whitfijs-jw/Volvo240-DigitalDash/QtDash/140 Ralleye Gauges/140-5ga-kmh-set.jpg

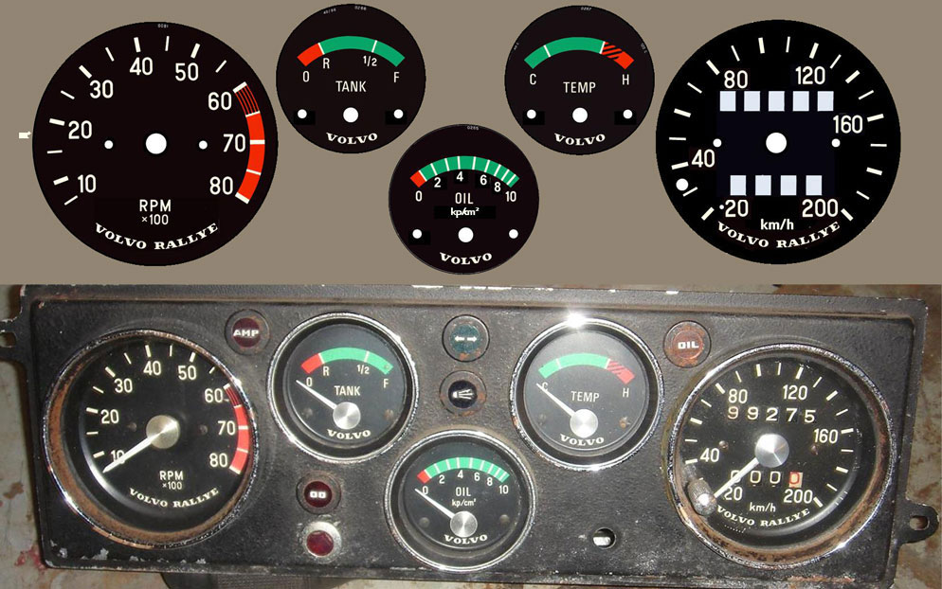
QtDash/140 Ralleye Gauges/140-5ga-kmh-set.jpg
