whitfijs-jw/Volvo240-DigitalDash/QtDash/140 Ralleye Gauges/140-5ga-mph-set.jpg

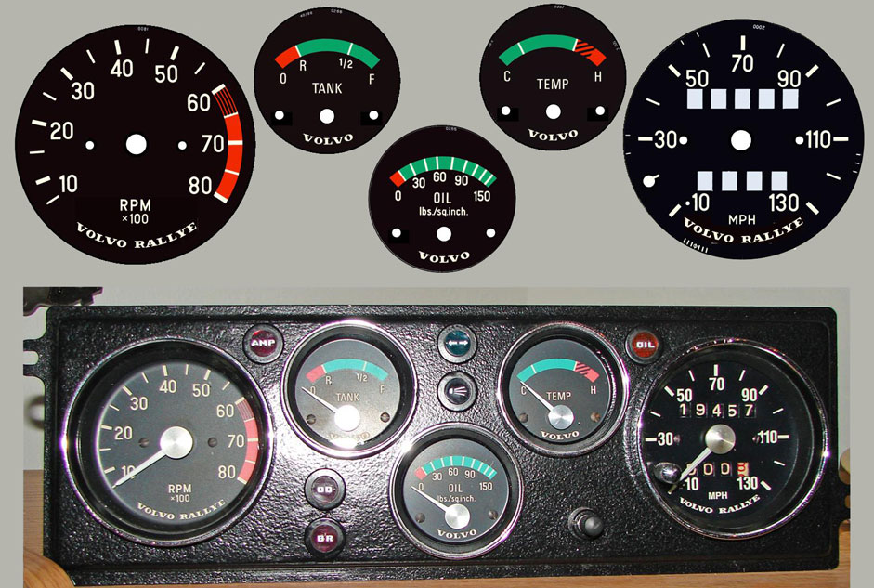
QtDash/140 Ralleye Gauges/140-5ga-mph-set.jpg
