whitfijs-jw/Volvo240-DigitalDash/QtDash/140 Ralleye Gauges/140-rallye-voltmeter.png

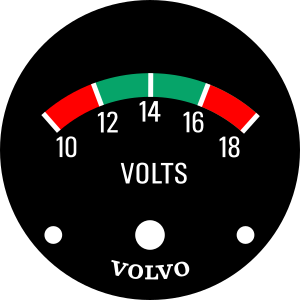
QtDash/140 Ralleye Gauges/140-rallye-voltmeter.png
