whitfijs-jw/Volvo240-DigitalDash/QtDash/240 gauges/81-85_240_220kmh04lo.png

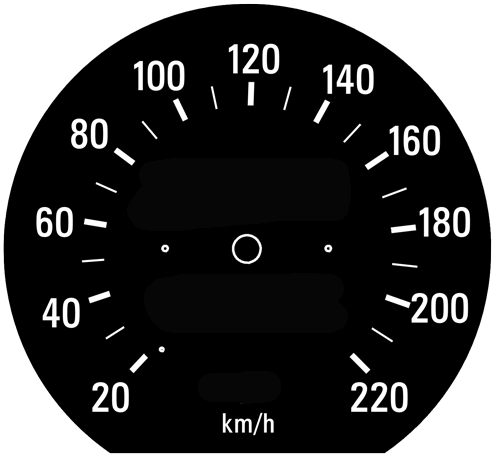
QtDash/240 gauges/81-85_240_220kmh04lo.png
