whitfijs-jw/Volvo240-DigitalDash/QtDash/240 gauges/early200kmhspeedolo.png

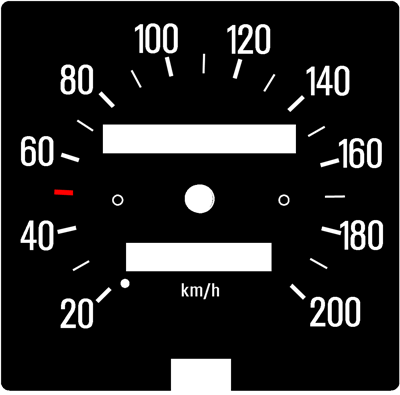
QtDash/240 gauges/early200kmhspeedolo.png
