whitfijs-jw/Volvo240-DigitalDash/QtDash/240 gauges/early-240-temp-fuel-overlay.png

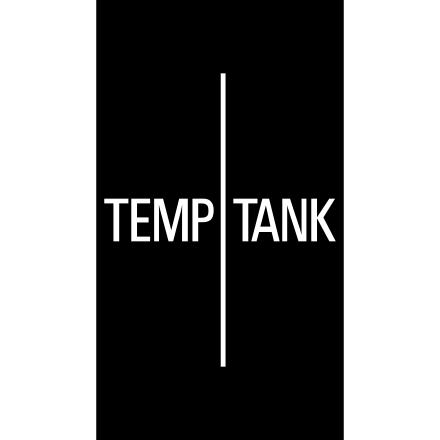
QtDash/240 gauges/early-240-temp-fuel-overlay.png
