whitfijs-jw/Volvo240-DigitalDash/QtDash/240 gauges/later-240-speedo-kph.png

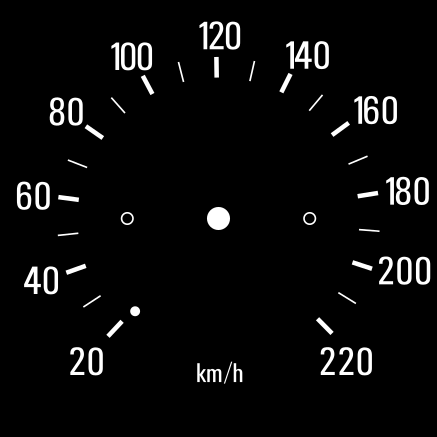
QtDash/240 gauges/later-240-speedo-kph.png
