whitfijs-jw/Volvo240-DigitalDash/QtDash/544 Gauges/oil-pressure-544-psi.png

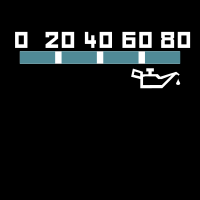
QtDash/544 Gauges/oil-pressure-544-psi.png
