whitfijs-jw/Volvo240-DigitalDash/QtDash/544 Gauges/PV-gaugecluster4-remote.jpg

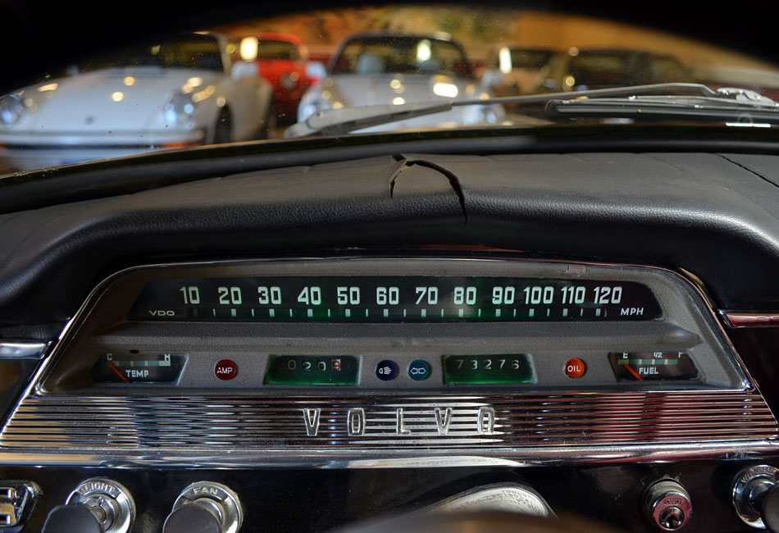
QtDash/544 Gauges/PV-gaugecluster4-remote.jpg
