whitfijs-jw/Volvo240-DigitalDash/QtDash/544 Gauges/s-l1600.jpg

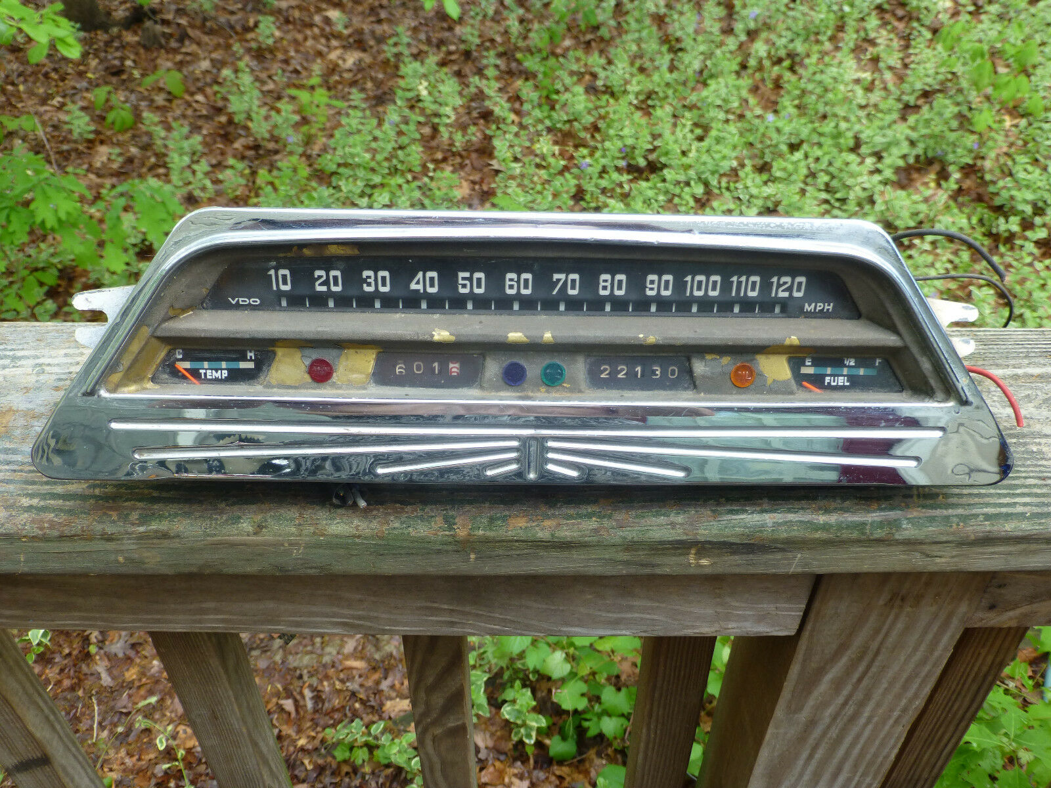
QtDash/544 Gauges/s-l1600.jpg
