whitfijs-jw/Volvo240-DigitalDash/QtDash/850R gauges/white_faces.jpg

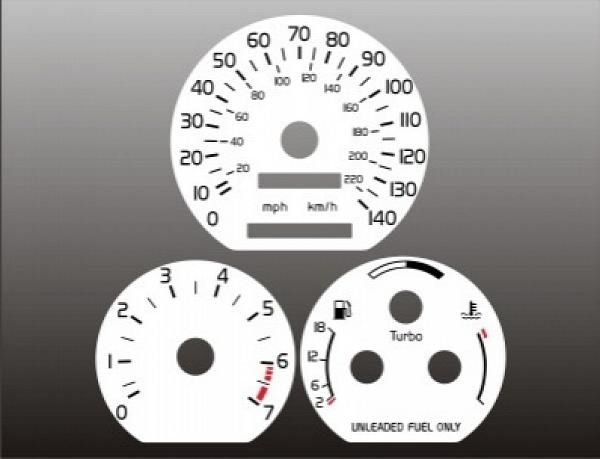
QtDash/850R gauges/white_faces.jpg
