whitfijs-jw/Volvo240-DigitalDash/QtDash/850R gauges/whole-dash.jpeg

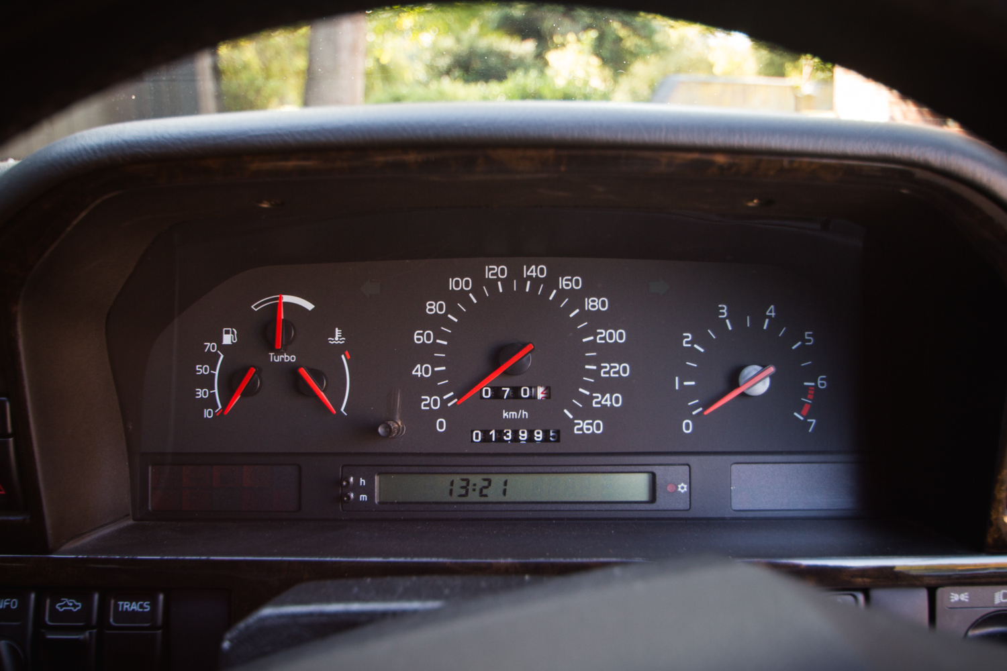
QtDash/850R gauges/whole-dash.jpeg
