whitfijs-jw/Volvo240-DigitalDash/QtDash/940 Gauges/740_boost.png

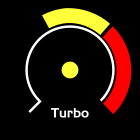
QtDash/940 Gauges/740_boost.png
