whitfijs-jw/Volvo240-DigitalDash/QtDash/940 Gauges/740_coolant_temp.png

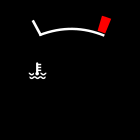
QtDash/940 Gauges/740_coolant_temp.png
