whitfijs-jw/Volvo240-DigitalDash/QtDash/940 Gauges/740_speedo_recreation.png

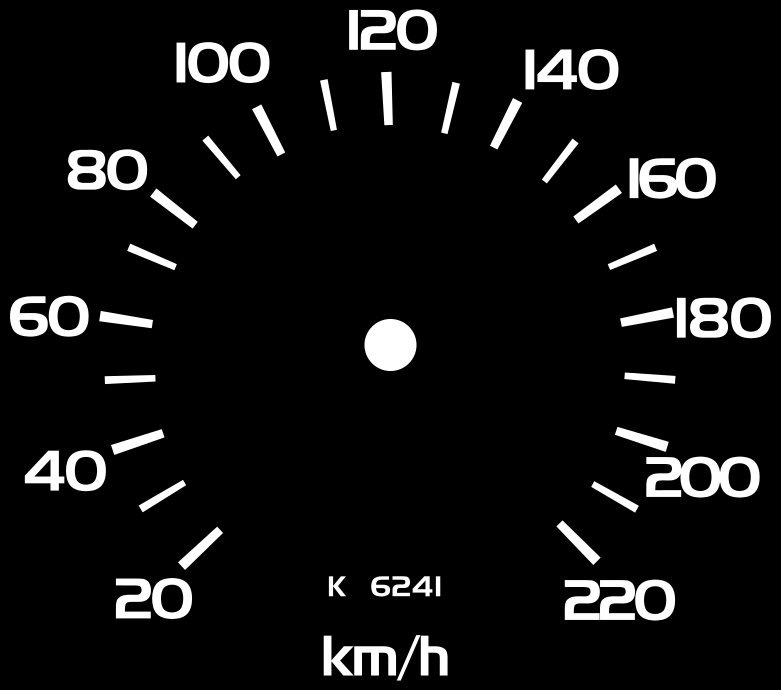
QtDash/940 Gauges/740_speedo_recreation.png
