whitfijs-jw/Volvo240-DigitalDash/QtDash/940 Gauges/740_tach.png

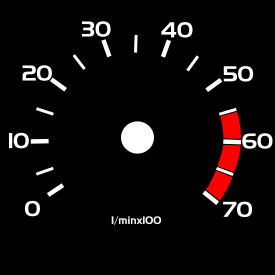
QtDash/940 Gauges/740_tach.png
