whitfijs-jw/Volvo240-DigitalDash/QtDash/940 Gauges/740_whole_dash.jpg

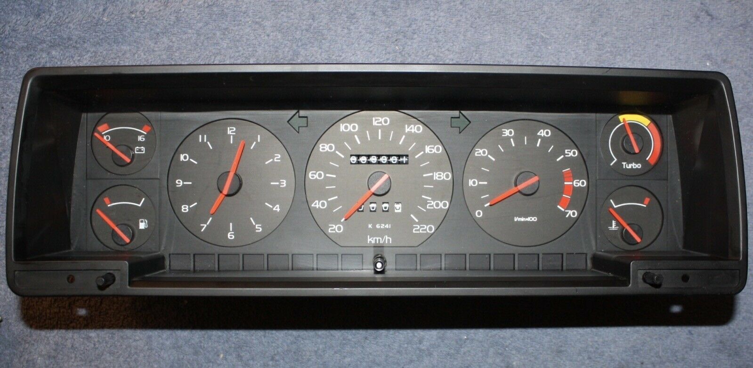
QtDash/940 Gauges/740_whole_dash.jpg
