whitfijs-jw/Volvo240-DigitalDash/QtDash/940 Gauges/940_turbo_cluster.png

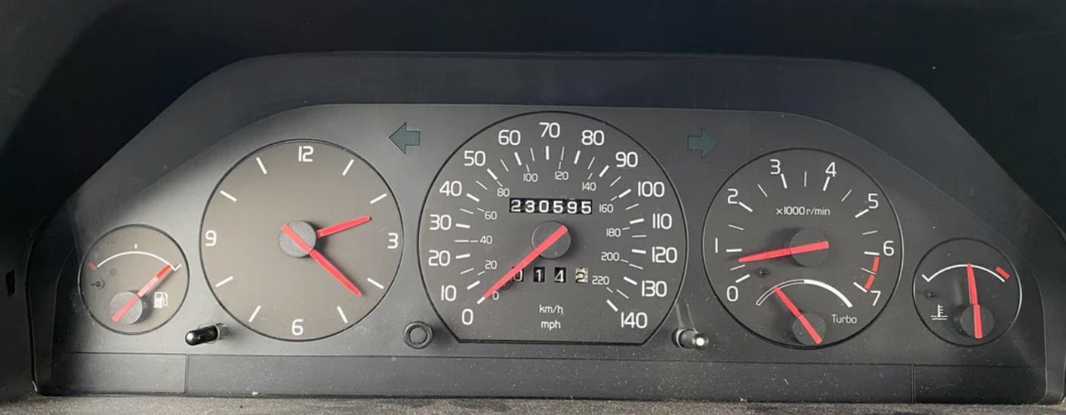
QtDash/940 Gauges/940_turbo_cluster.png
