whitfijs-jw/Volvo240-DigitalDash/QtDash/940 Gauges/clock_940.jpg

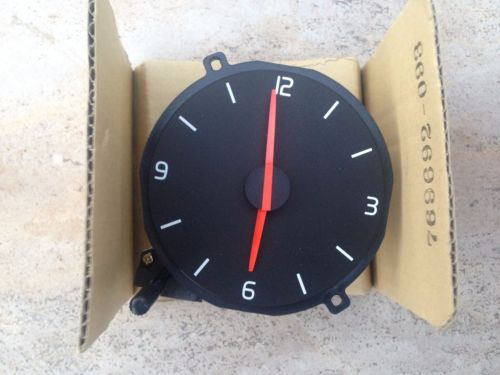
QtDash/940 Gauges/clock_940.jpg
