whitfijs-jw/Volvo240-DigitalDash/QtDash/940 Gauges/speedo4.JPG

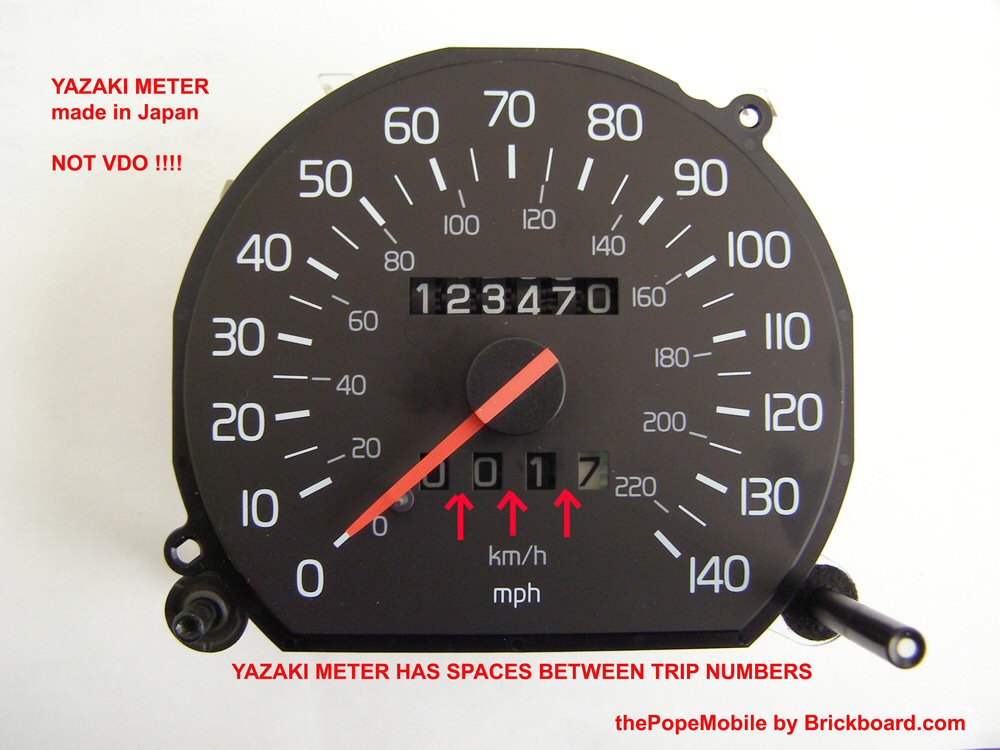
QtDash/940 Gauges/speedo4.JPG
