whitfijs-jw/Volvo240-DigitalDash/QtDash/940 Gauges/speedo_940.jpg

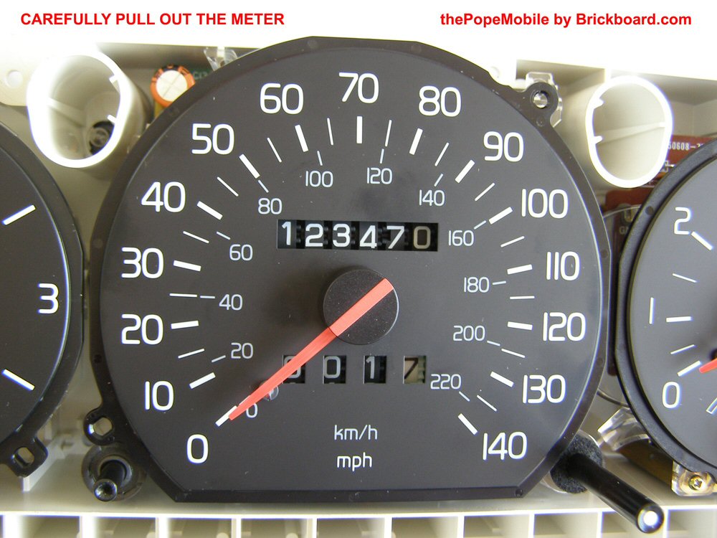
QtDash/940 Gauges/speedo_940.jpg
