whitfijs-jw/Volvo240-DigitalDash/QtDash/940 Gauges/whole_dash.jpeg

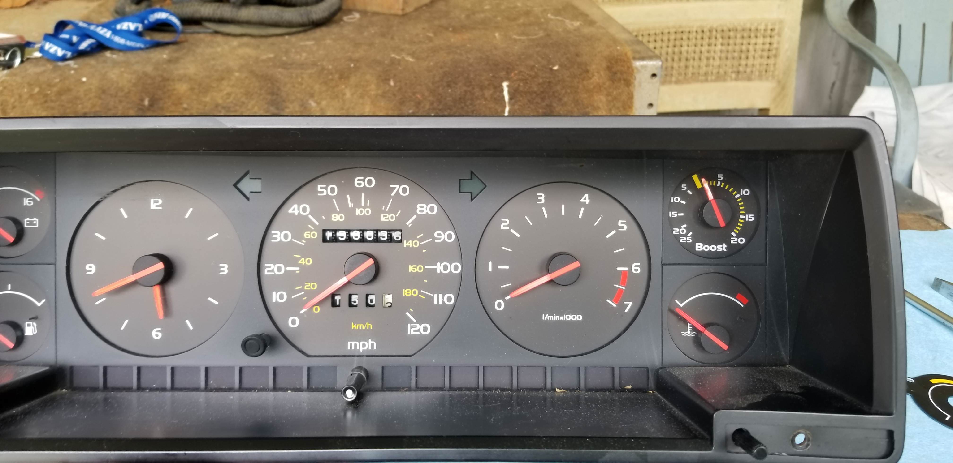
QtDash/940 Gauges/whole_dash.jpeg
