whitfijs-jw/Volvo240-DigitalDash/QtDash/Hardware/Dash Pinouts/240instruments1980med.jpg

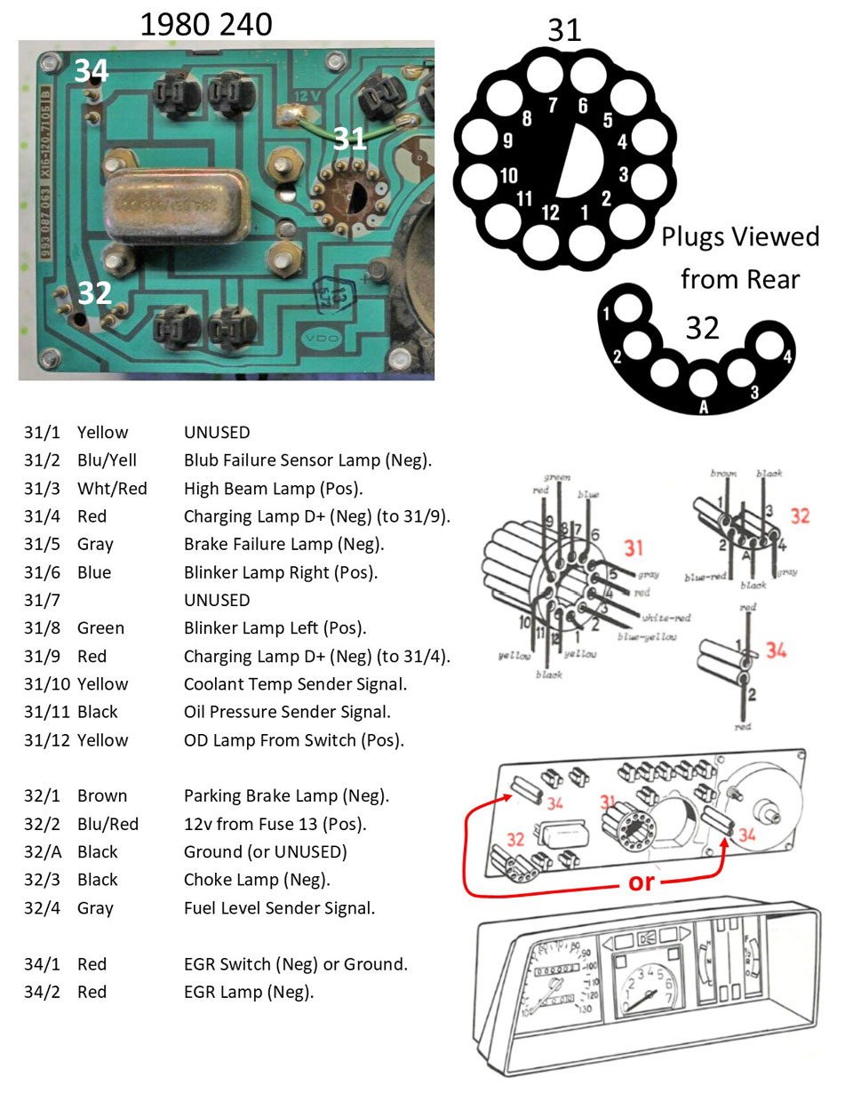
QtDash/Hardware/Dash Pinouts/240instruments1980med.jpg
