whitfijs-jw/Volvo240-DigitalDash/QtDash/Hardware/Dash Pinouts/240instruments1984-01med.jpg

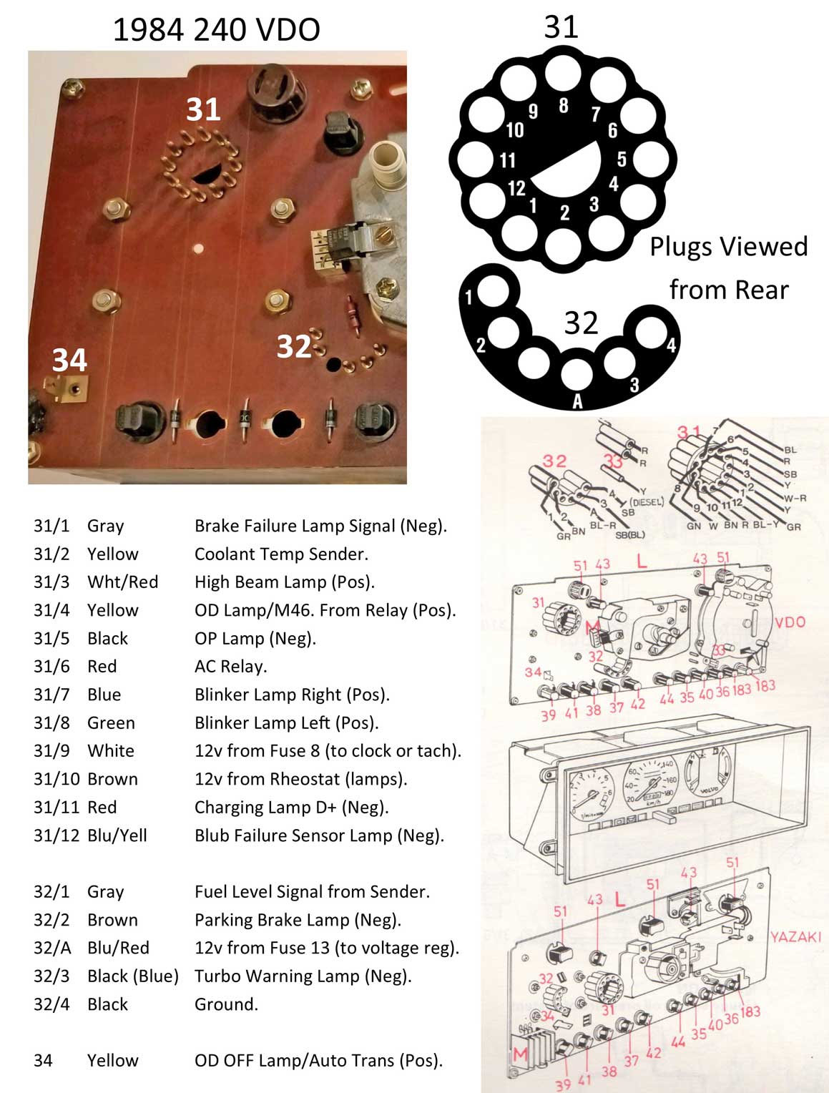
QtDash/Hardware/Dash Pinouts/240instruments1984-01med.jpg
