whitfijs-jw/Volvo240-DigitalDash/QtDash/Hardware/Dash Pinouts/240instruments1987-01med.jpg

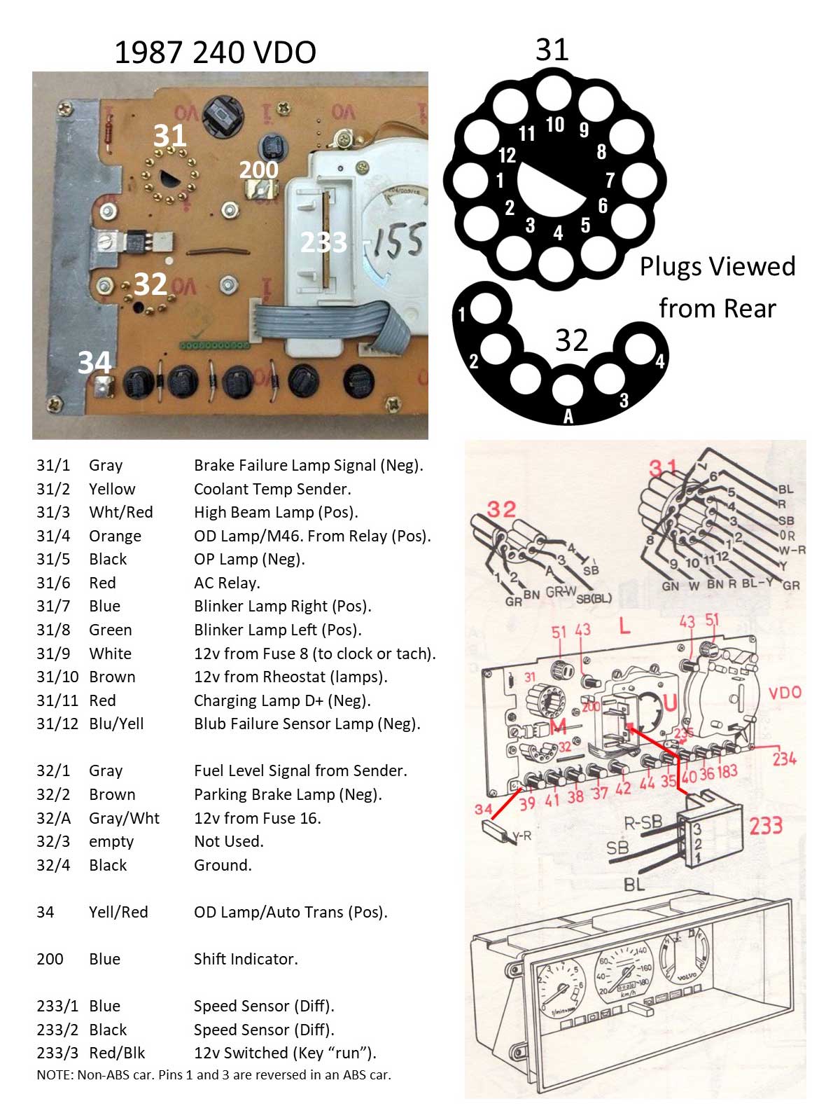
QtDash/Hardware/Dash Pinouts/240instruments1987-01med.jpg
