whitfijs-jw/Volvo240-DigitalDash/QtDash/Hardware/Dash Pinouts/240instruments1993-002med.jpg

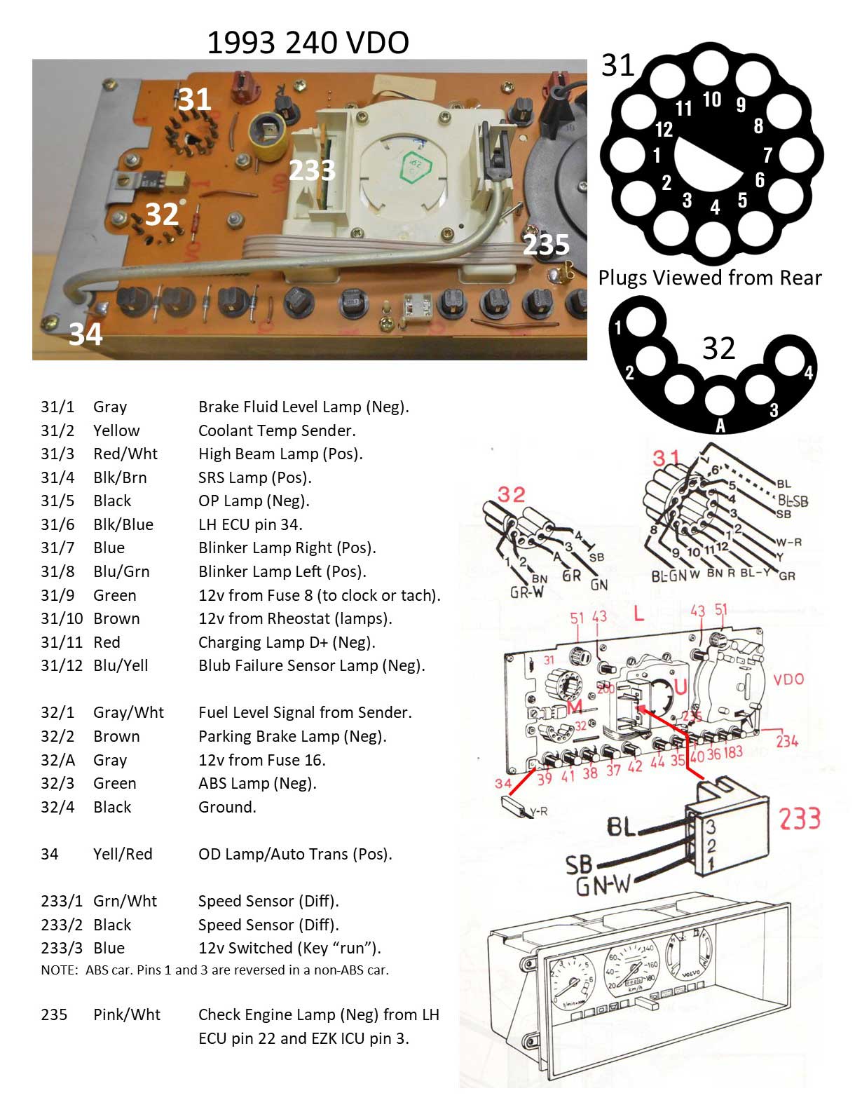
QtDash/Hardware/Dash Pinouts/240instruments1993-002med.jpg
