whitfijs-jw/Volvo240-DigitalDash/QtDash/Hardware/Dash Pinouts/240instruments-rsport-2med.jpg

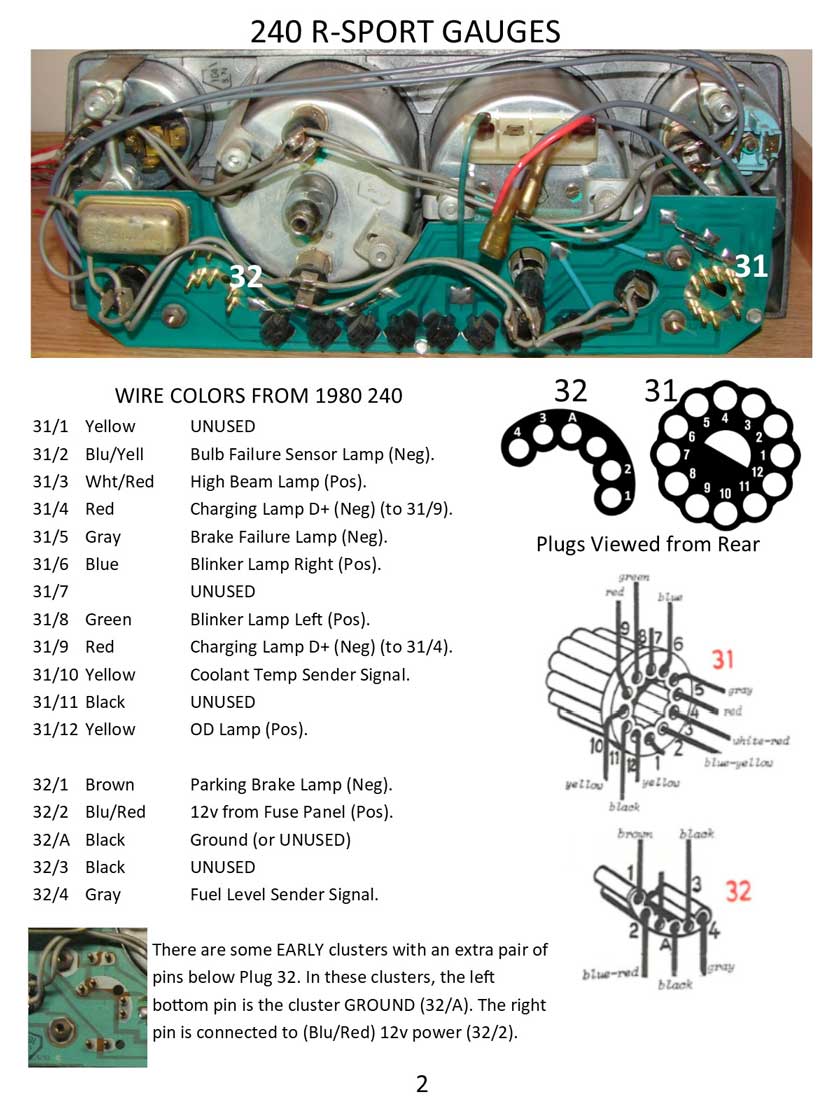
QtDash/Hardware/Dash Pinouts/240instruments-rsport-2med.jpg
