whitfijs-jw/Volvo240-DigitalDash/QtDash/Hardware/DashHat/Board Previews/Rev C/bottom.png

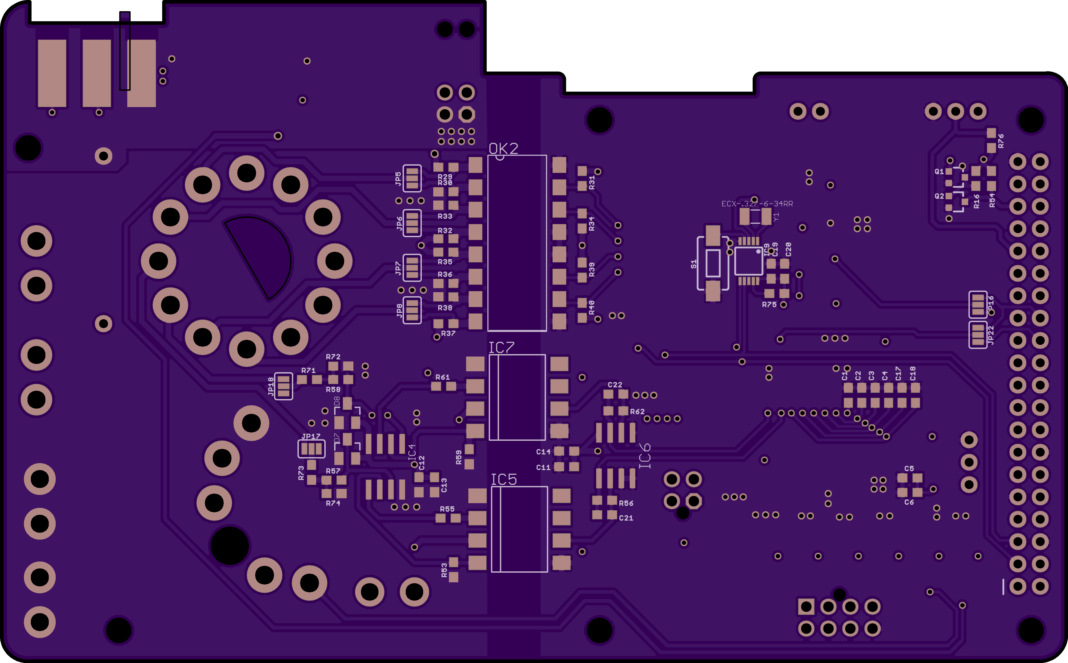
QtDash/Hardware/DashHat/Board Previews/Rev C/bottom.png
