whitfijs-jw/Volvo240-DigitalDash/QtDash/Hardware/DashHat/Board Previews/Rev C/top.png

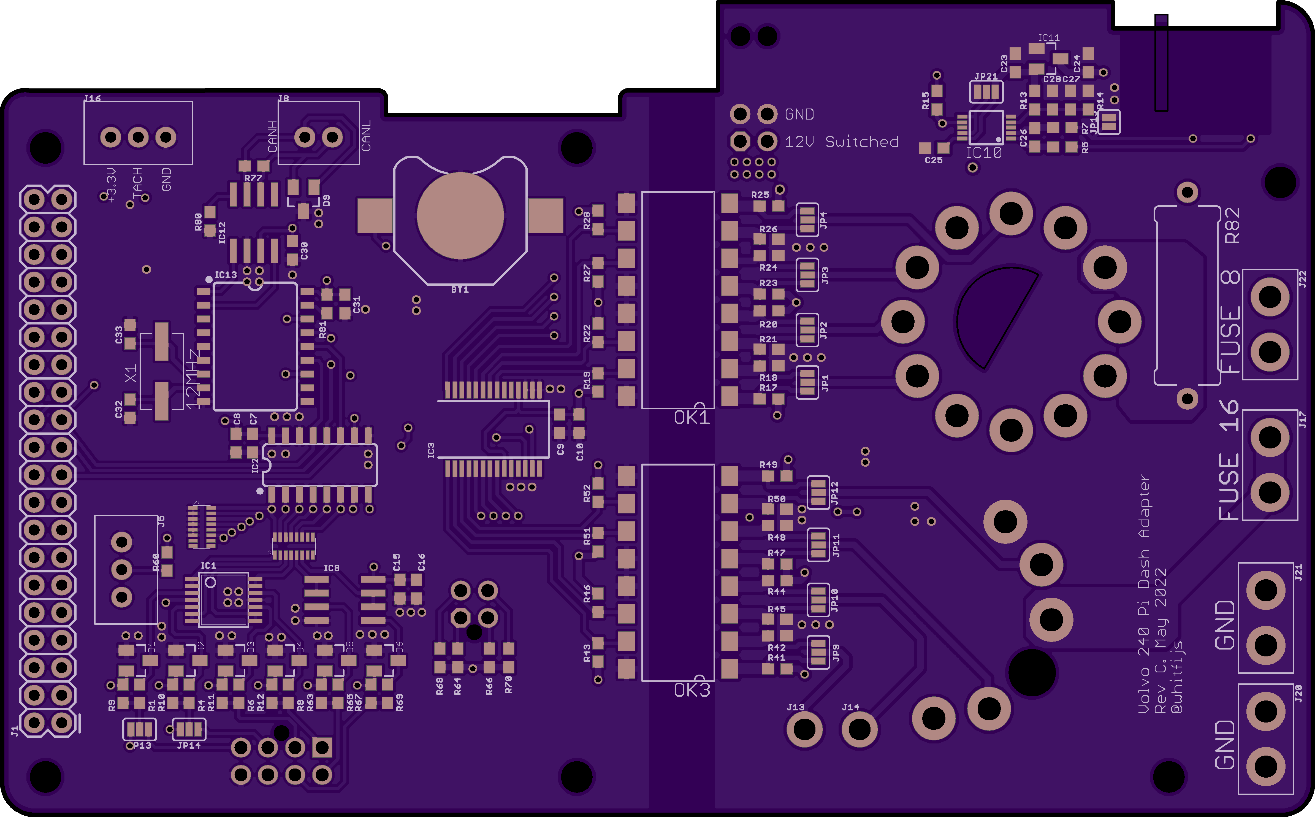
QtDash/Hardware/DashHat/Board Previews/Rev C/top.png
