whitfijs-jw/Volvo240-DigitalDash/QtDash/Hardware/Datasheets/Sensor Info/gm_MAP_sensors.gif

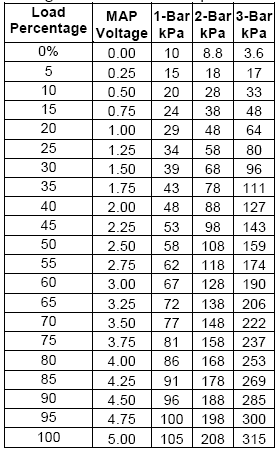
QtDash/Hardware/Datasheets/Sensor Info/gm_MAP_sensors.gif
