whitfijs-jw/Volvo240-DigitalDash/QtDash/Hardware/TouchPanel/3D Models/back_both_covers.png

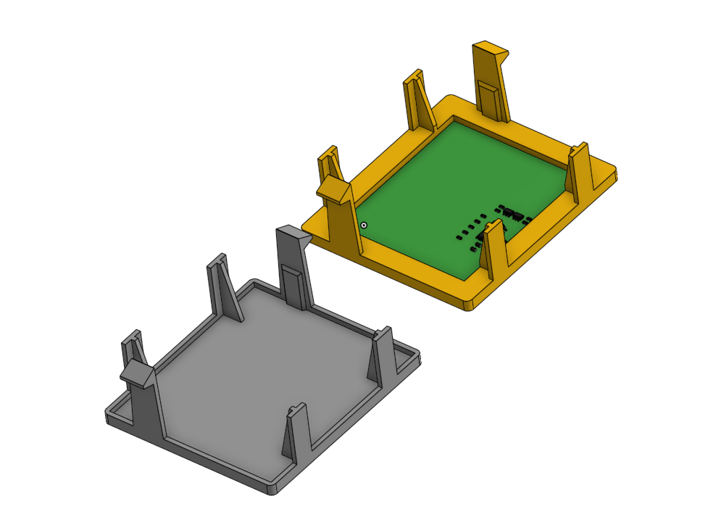
QtDash/Hardware/TouchPanel/3D Models/back_both_covers.png
