whitfijs-jw/Volvo240-DigitalDash/QtDash/Hardware/TouchPanel/touch_panel/bottom_layer.svg/g48.png

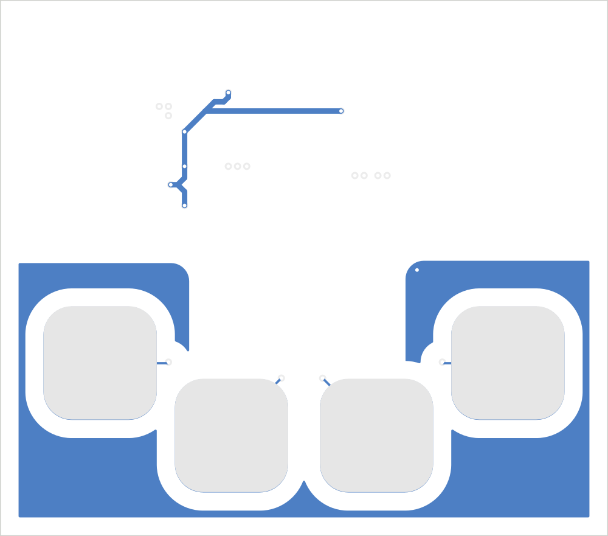
QtDash/Hardware/TouchPanel/touch_panel/bottom_layer.svg/g48.png
