whitfijs-jw/Volvo240-DigitalDash/QtDash/p1800 Gauges/2v2ucAjL2x37gRP.jpg

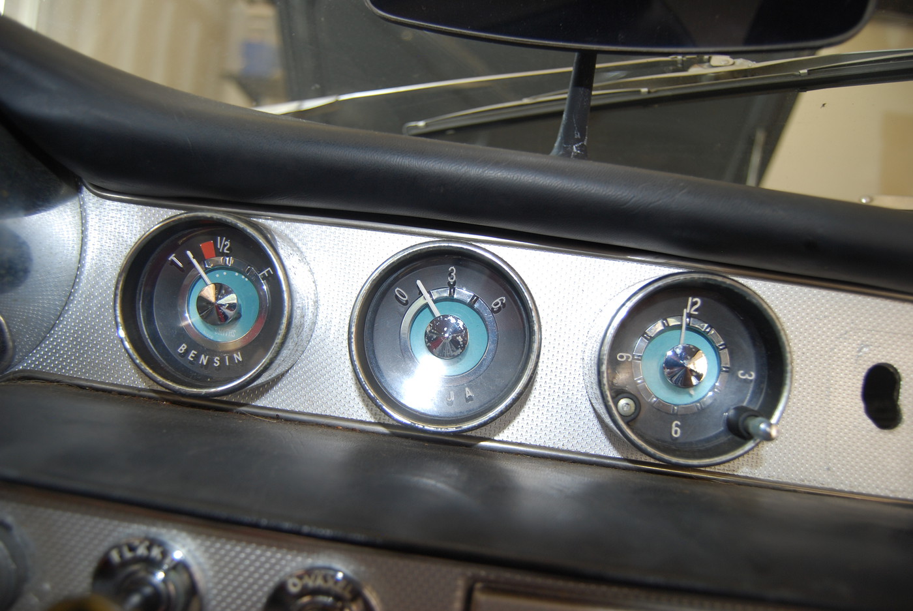
QtDash/p1800 Gauges/2v2ucAjL2x37gRP.jpg
