whitfijs-jw/Volvo240-DigitalDash/QtDash/p1800 Gauges/2v2ucBK9Ux37gRP.jpg

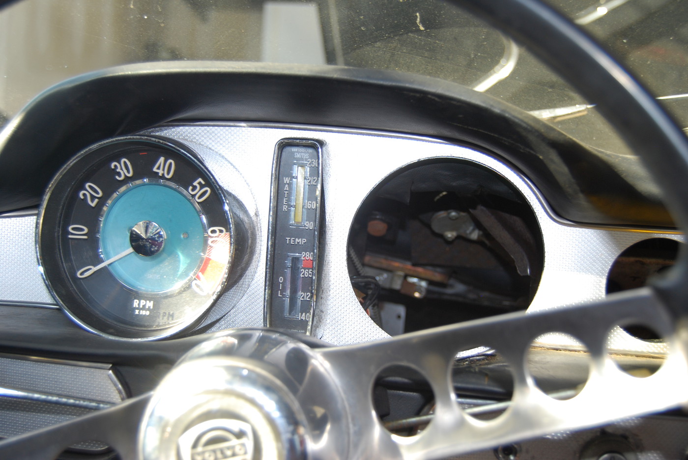
QtDash/p1800 Gauges/2v2ucBK9Ux37gRP.jpg
