whitfijs-jw/Volvo240-DigitalDash/QtDash/p1800 Gauges/1964-volvo-p1800-s-coupe-photo-board.jpg

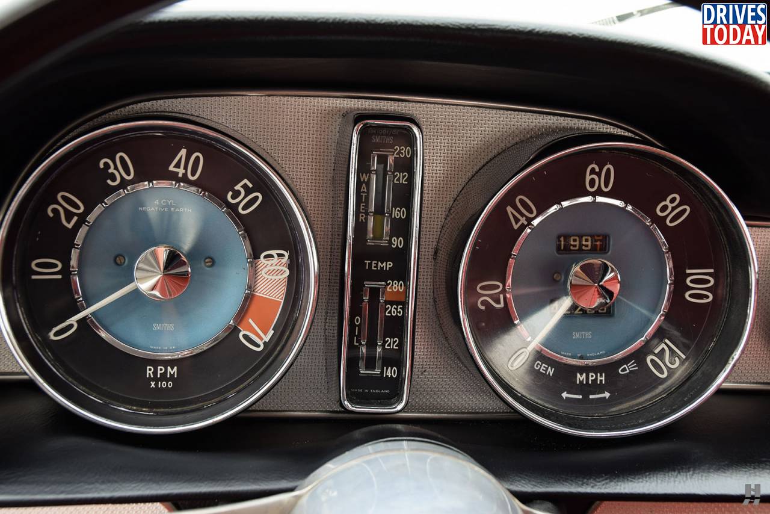
QtDash/p1800 Gauges/1964-volvo-p1800-s-coupe-photo-board.jpg
