whitfijs-jw/Volvo240-DigitalDash/QtDash/p1800 Gauges/1973-volvo-1800-es.jpeg

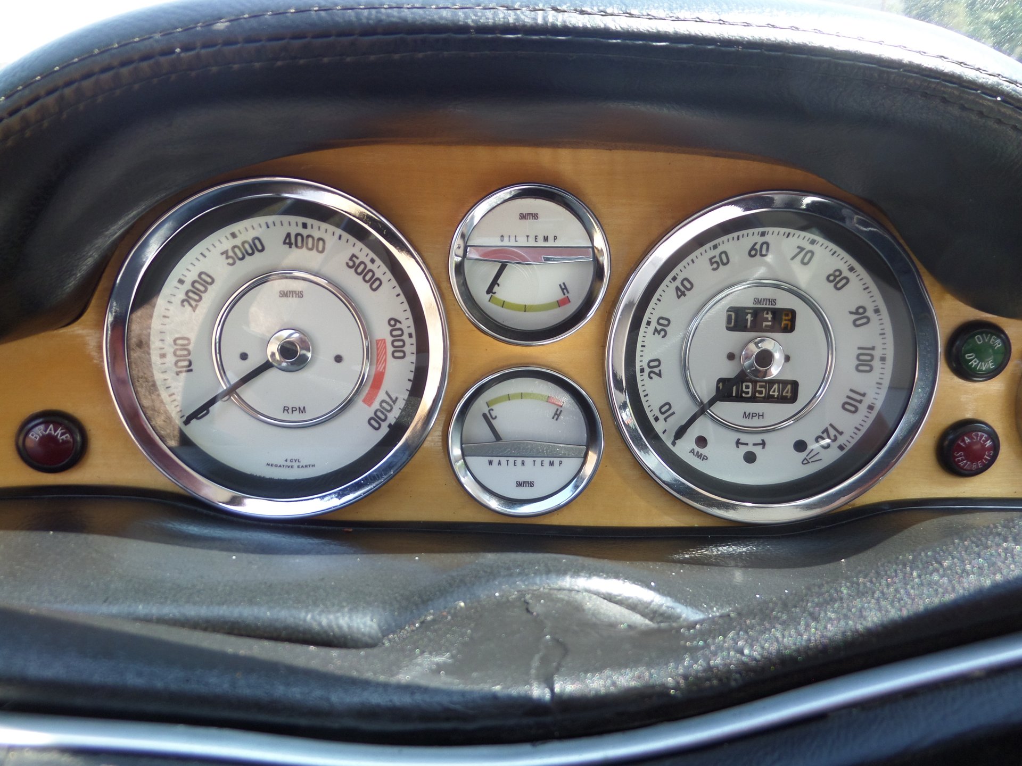
QtDash/p1800 Gauges/1973-volvo-1800-es.jpeg
