whitfijs-jw/Volvo240-DigitalDash/QtDash/p1800 Gauges/6059_9.jpg

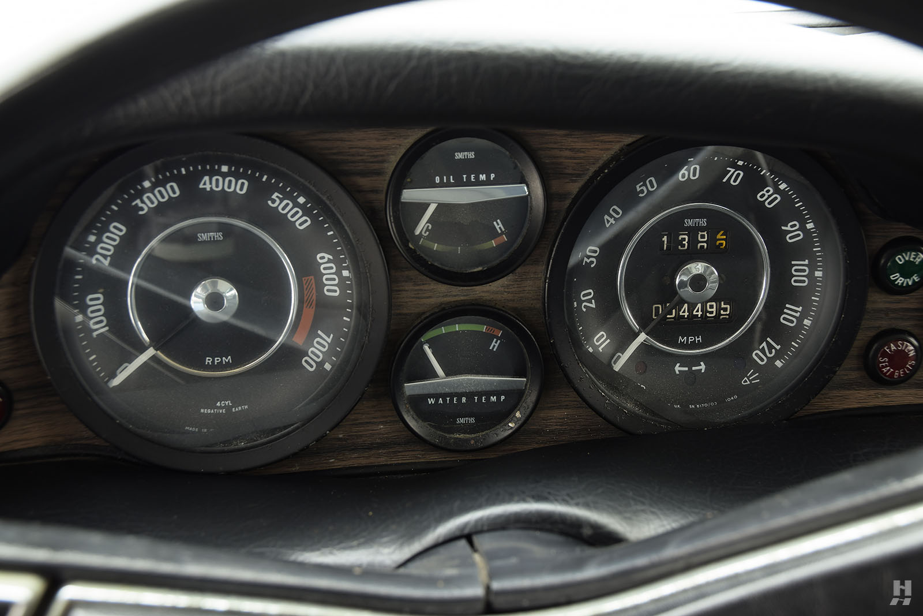
QtDash/p1800 Gauges/6059_9.jpg
