whitfijs-jw/Volvo240-DigitalDash/QtDash/p1800 Gauges/25753.jpg

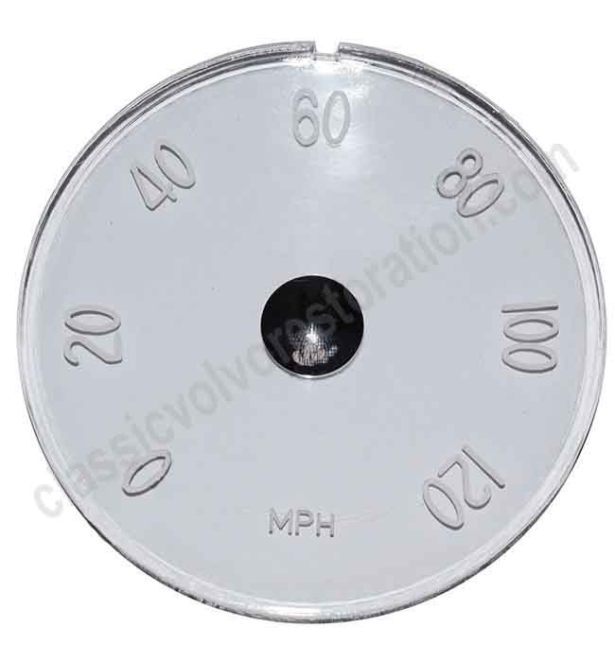
QtDash/p1800 Gauges/25753.jpg
