whitfijs-jw/Volvo240-DigitalDash/QtDash/p1800 Gauges/CC210-RESTO-1962Volvo-2-instruments-rebuilt.jpg

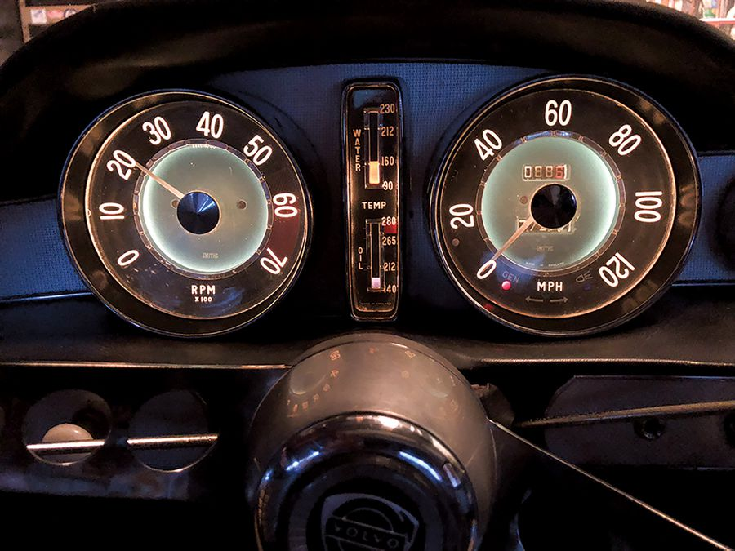
QtDash/p1800 Gauges/CC210-RESTO-1962Volvo-2-instruments-rebuilt.jpg
