whitfijs-jw/Volvo240-DigitalDash/QtDash/p1800 Gauges/fuel-level-p1800.png

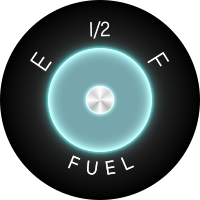
QtDash/p1800 Gauges/fuel-level-p1800.png
