whitfijs-jw/Volvo240-DigitalDash/QtDash/p1800 Gauges/index.jpeg

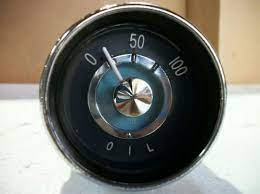
QtDash/p1800 Gauges/index.jpeg
