whitfijs-jw/Volvo240-DigitalDash/QtDash/p1800 Gauges/Smith_tach_gen2_face.jpg

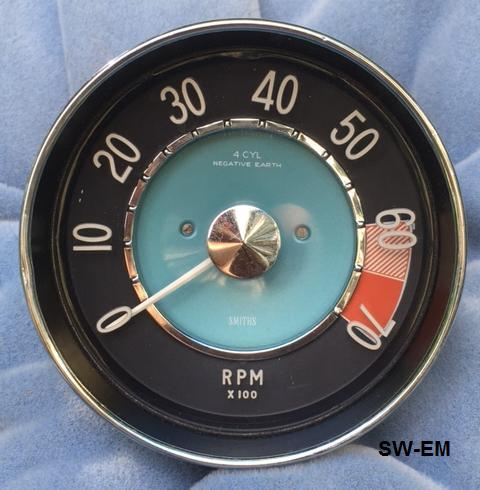
QtDash/p1800 Gauges/Smith_tach_gen2_face.jpg
