whitfijs-jw/Volvo240-DigitalDash/QtDash/p1800 Gauges/VolvoP1800-0887-1.webp

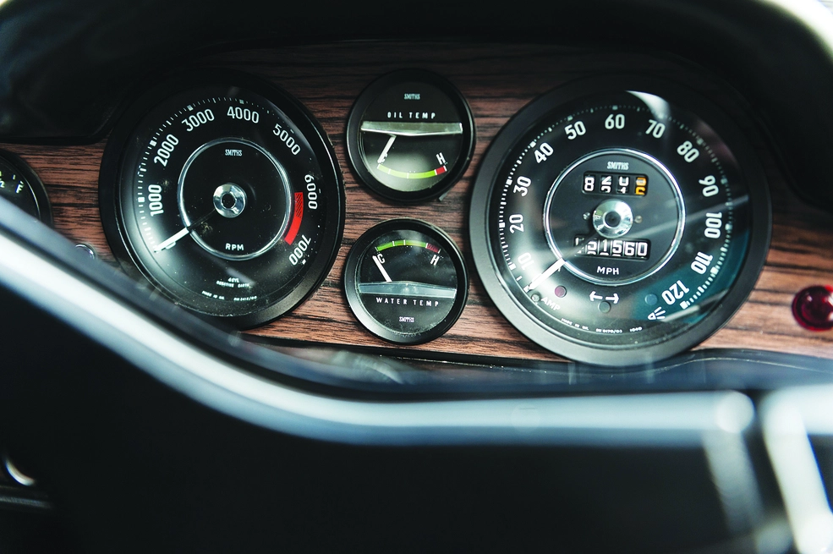
QtDash/p1800 Gauges/VolvoP1800-0887-1.webp
