whitfijs-jw/Volvo240-DigitalDash/QtDash/Pictures/240-clock-dual-screen.jpg

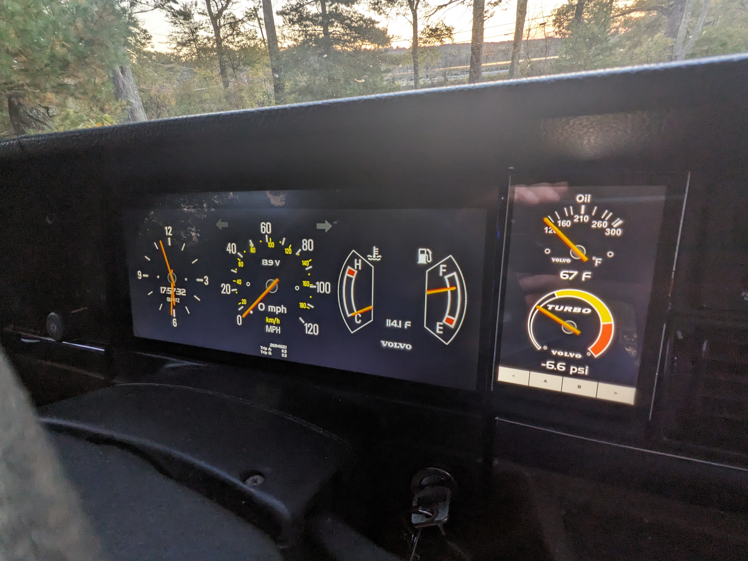
QtDash/Pictures/240-clock-dual-screen.jpg
