whitfijs-jw/Volvo240-DigitalDash/QtDash/Pictures/240-clock-single-screen.jpg

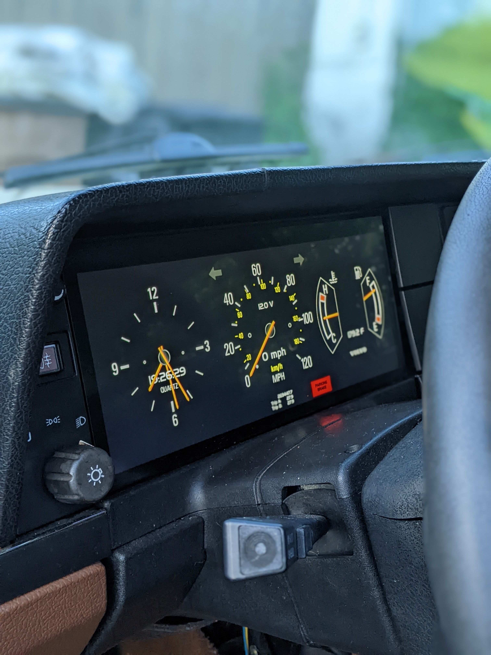
QtDash/Pictures/240-clock-single-screen.jpg
