whitfijs-jw/Volvo240-DigitalDash/QtDash/Pictures/240-custom-single-screen.jpg

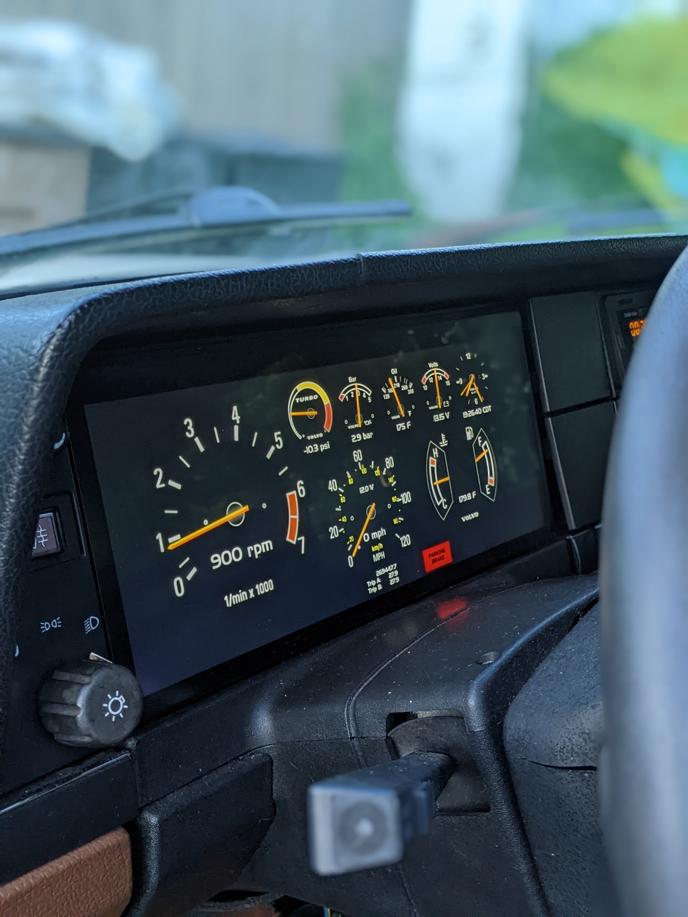
QtDash/Pictures/240-custom-single-screen.jpg
