whitfijs-jw/Volvo240-DigitalDash/QtDash/Pictures/240-custom-tach-center-single-screen.jpg

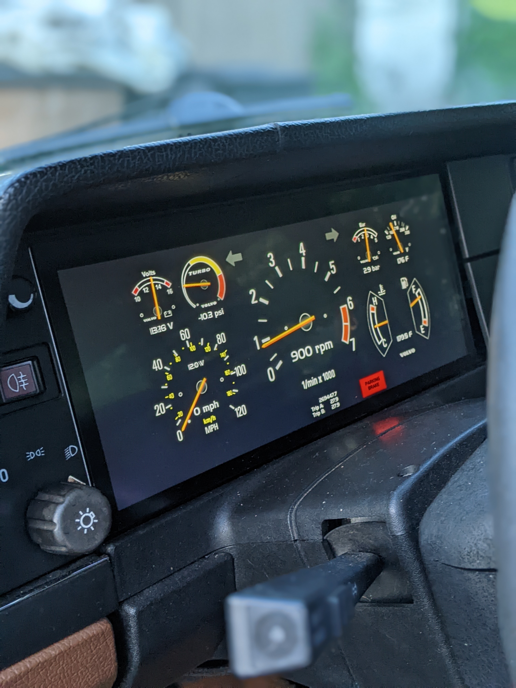
QtDash/Pictures/240-custom-tach-center-single-screen.jpg
