whitfijs-jw/Volvo240-DigitalDash/QtDash/Pictures/544-140-single-screen.jpg

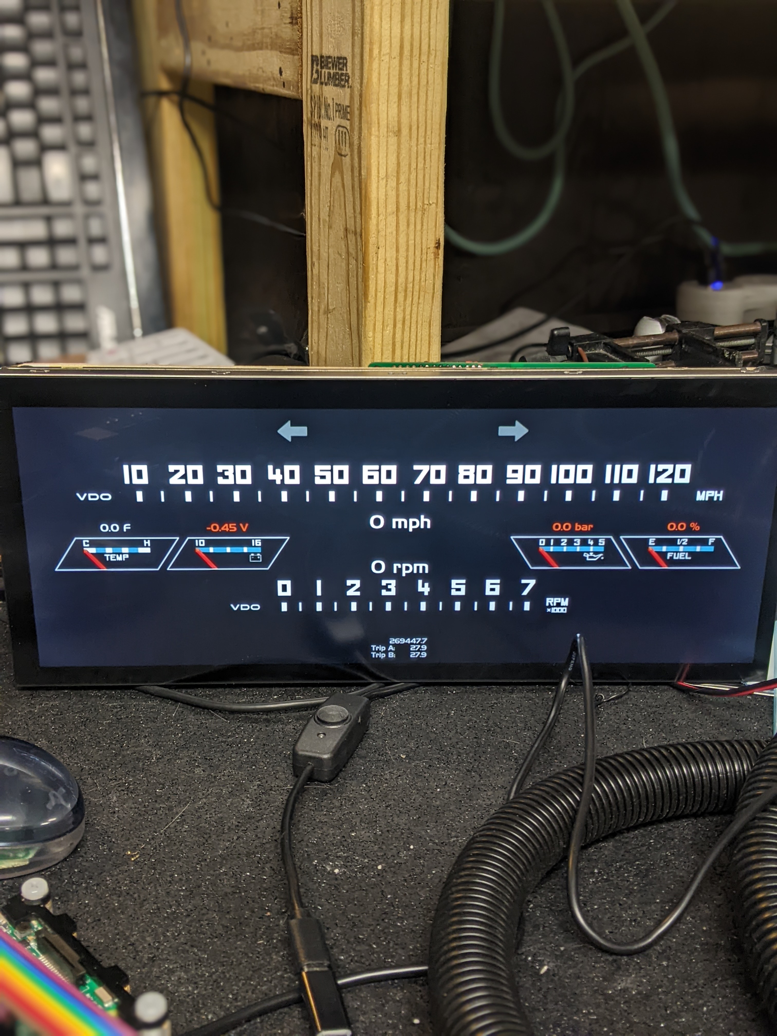
QtDash/Pictures/544-140-single-screen.jpg
