whitfijs-jw/Volvo240-DigitalDash/QtDash/Pictures/740-dual-screen.jpg

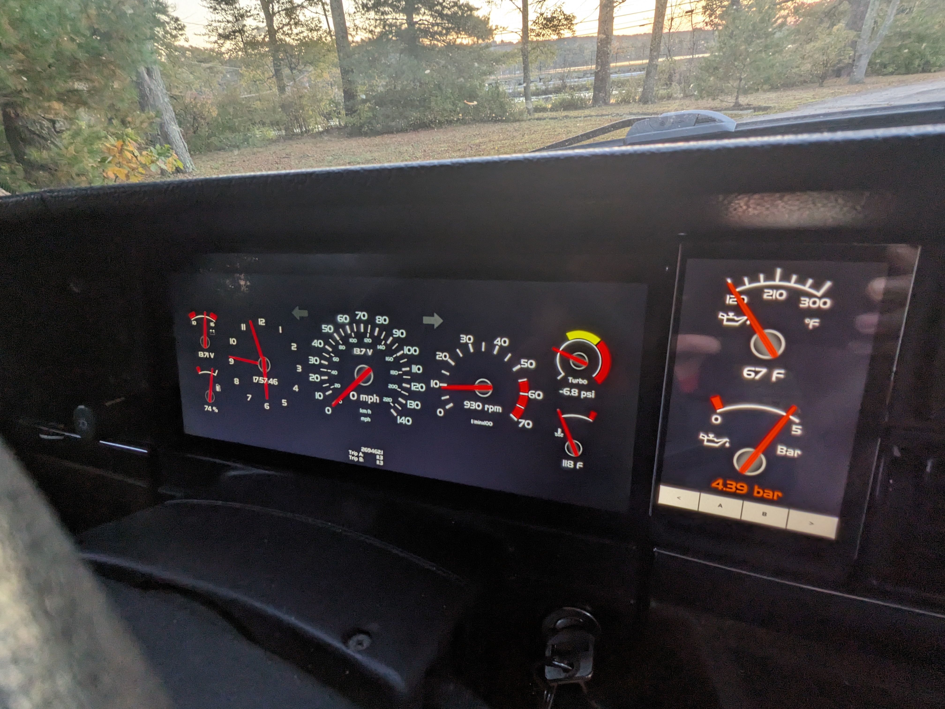
QtDash/Pictures/740-dual-screen.jpg
