whitfijs-jw/Volvo240-DigitalDash/QtDash/Pictures/740-single-screen.jpg

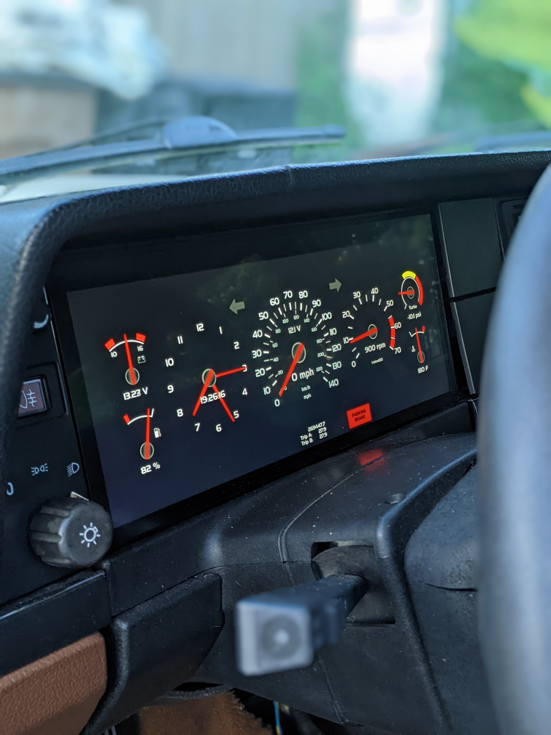
QtDash/Pictures/740-single-screen.jpg
