whitfijs-jw/Volvo240-DigitalDash/QtDash/Pictures/850R--single-screen.jpg

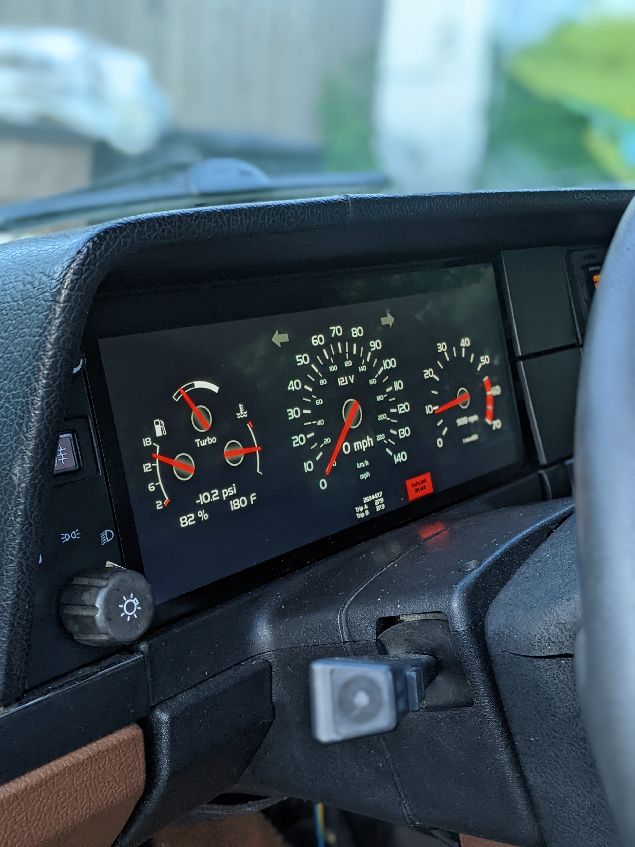
QtDash/Pictures/850R--single-screen.jpg
