whitfijs-jw/Volvo240-DigitalDash/QtDash/Pictures/850R-dual-screen.jpg

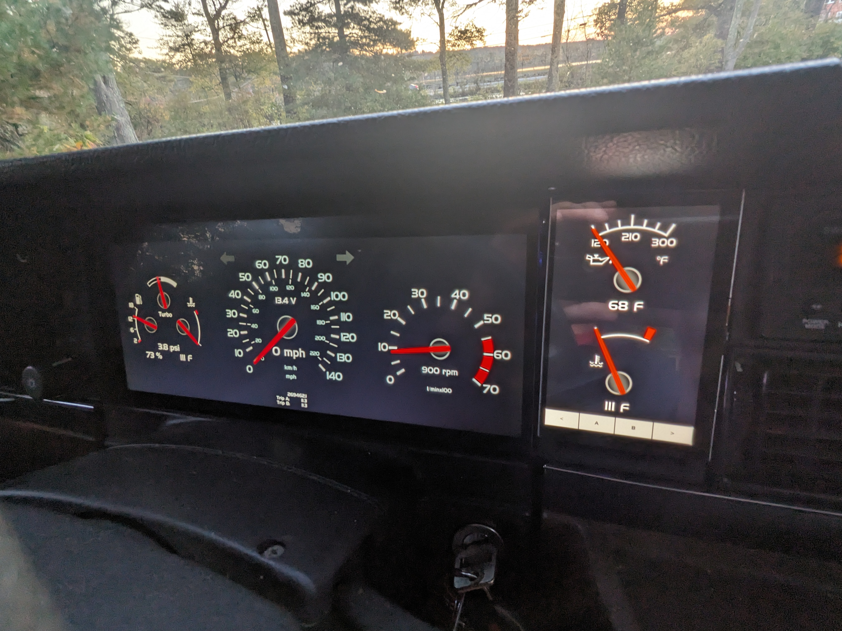
QtDash/Pictures/850R-dual-screen.jpg
