whitfijs-jw/Volvo240-DigitalDash/QtDash/Pictures/p1800-development.png

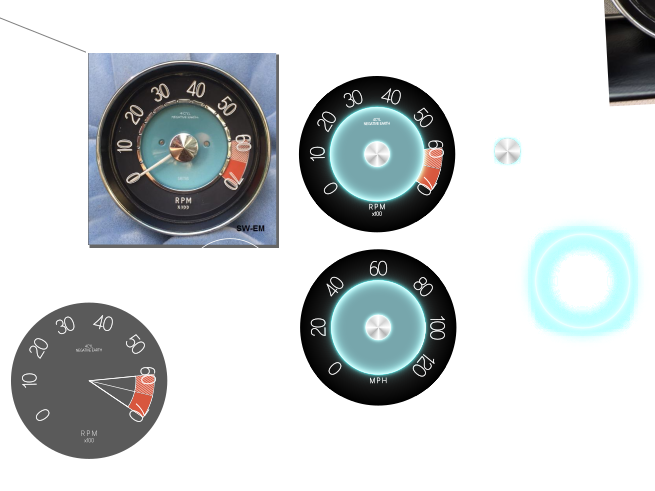
QtDash/Pictures/p1800-development.png
