whitfijs-jw/Volvo240-DigitalDash/QtDash/Pictures/p1800-dual-screen.jpg

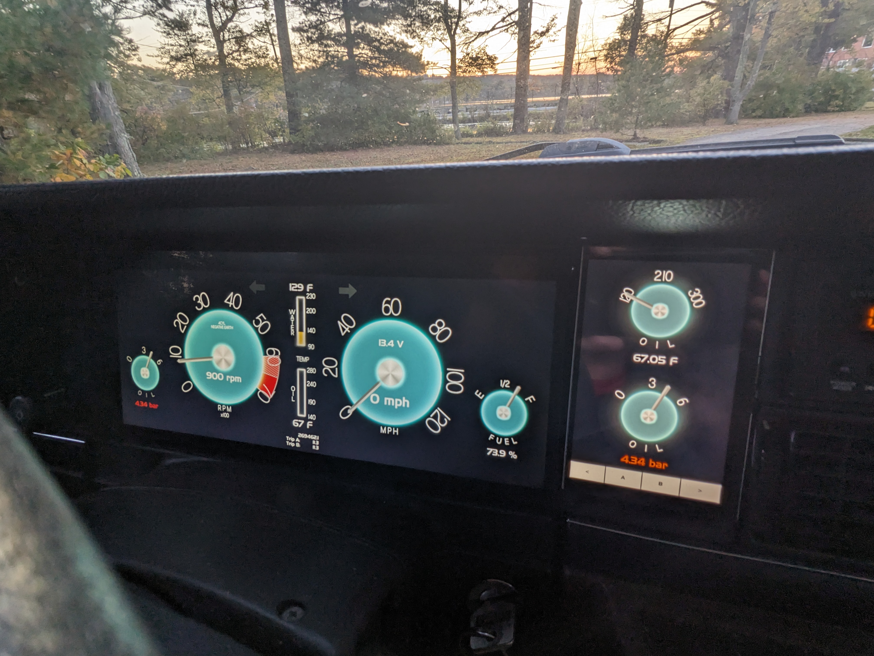
QtDash/Pictures/p1800-dual-screen.jpg
