whitfijs-jw/Volvo240-DigitalDash/QtDash/Pictures/rsport-single-screen.jpg

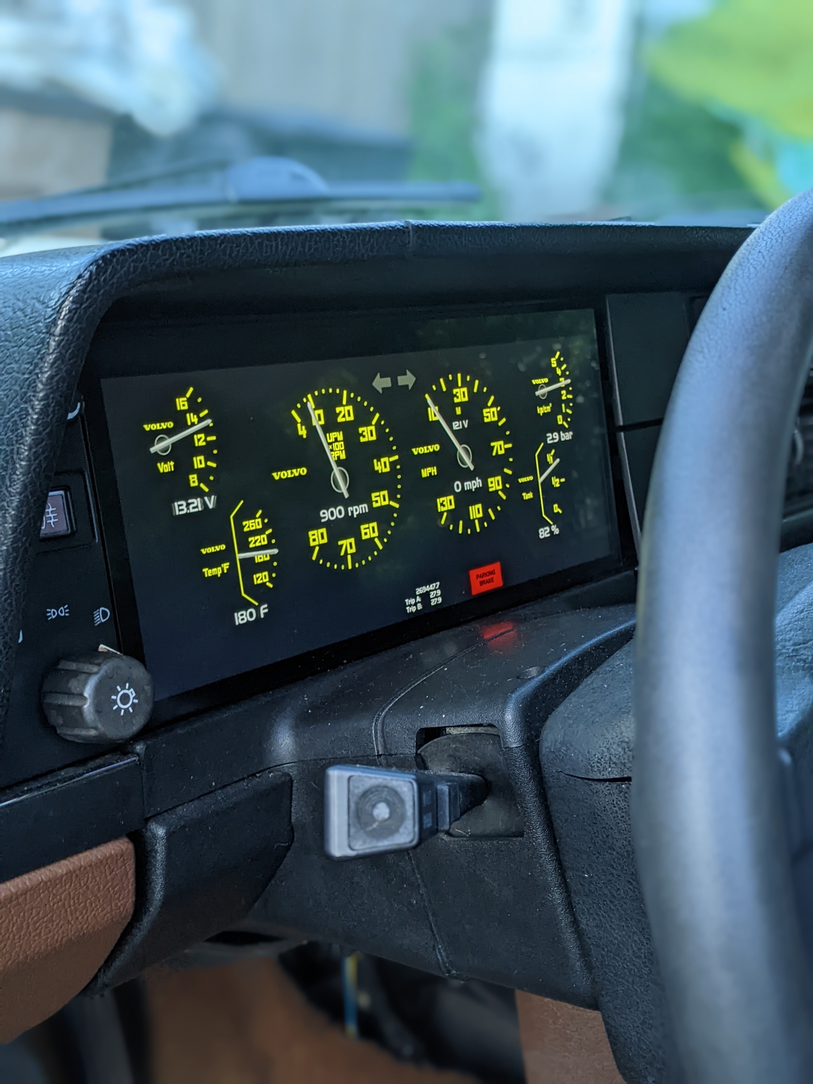
QtDash/Pictures/rsport-single-screen.jpg
