whitfijs-jw/Volvo240-DigitalDash/QtDash/project_preview.jpg

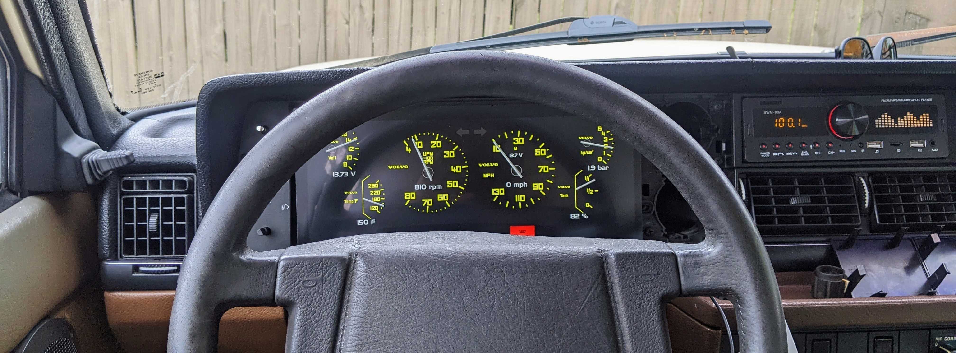
QtDash/project_preview.jpg
