whitfijs-jw/Volvo240-DigitalDash/QtDash/R-sport-cluster/r_sport_acc_coolant_fahrenhet.png

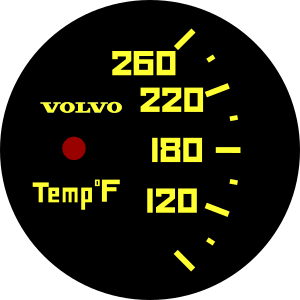
QtDash/R-sport-cluster/r_sport_acc_coolant_fahrenhet.png
