whitfijs-jw/Volvo240-DigitalDash/QtDash/R-sport-cluster/r_sport_oil_pressure_5bar.png

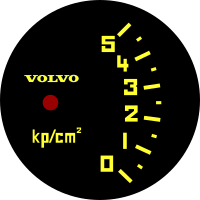
QtDash/R-sport-cluster/r_sport_oil_pressure_5bar.png
