whitfijs-jw/Volvo240-DigitalDash/QtDash/R-sport-cluster/r_sport_oil_temp_F.png

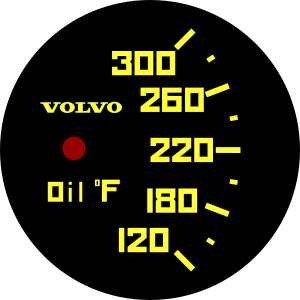
QtDash/R-sport-cluster/r_sport_oil_temp_F.png
