whitfijs-jw/Volvo240-DigitalDash/QtDash/s60R gauges/s-l1600.jpg

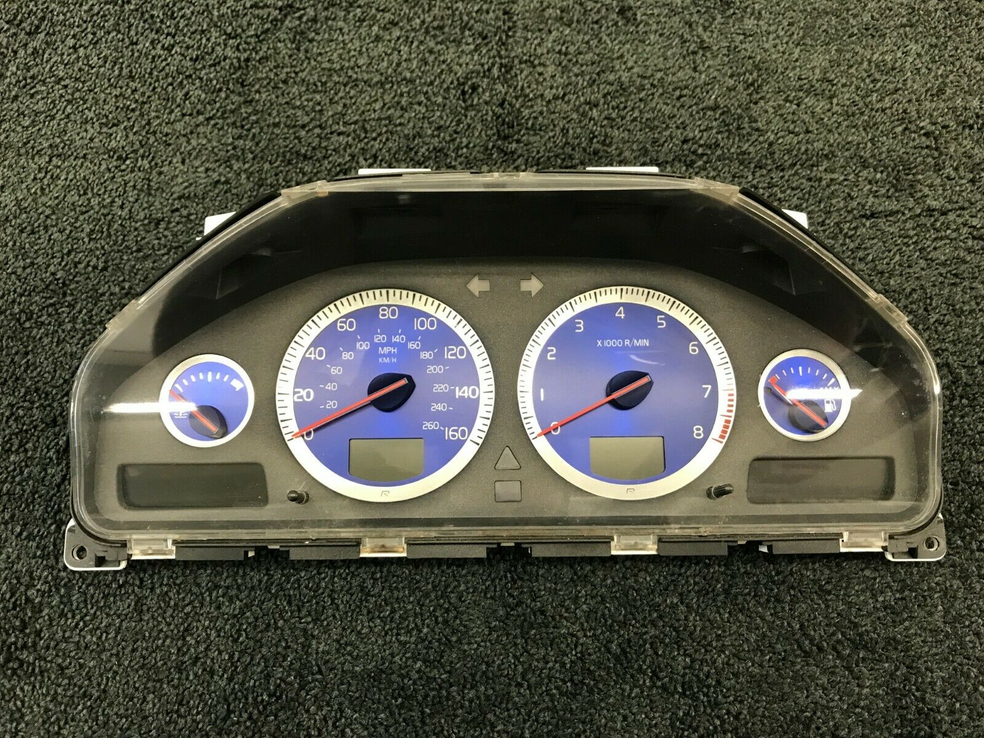
QtDash/s60R gauges/s-l1600.jpg
