whitfijs-jw/Volvo240-DigitalDash/QtDash/Hardware/Screen Mounting/Electronics Mount.stl

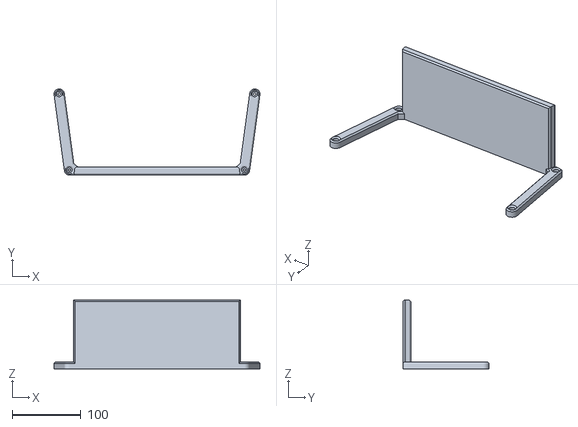
[picture p155: CAD file, 2022-02-13]
QtDash/Hardware/Screen Mounting/Electronics Mount.stl
298.8 x 125.1 x 100.0
