whitfijs-jw/Volvo240-DigitalDash/QtDash/Hardware/Screen Mounting/Electronics Mount-right.stl

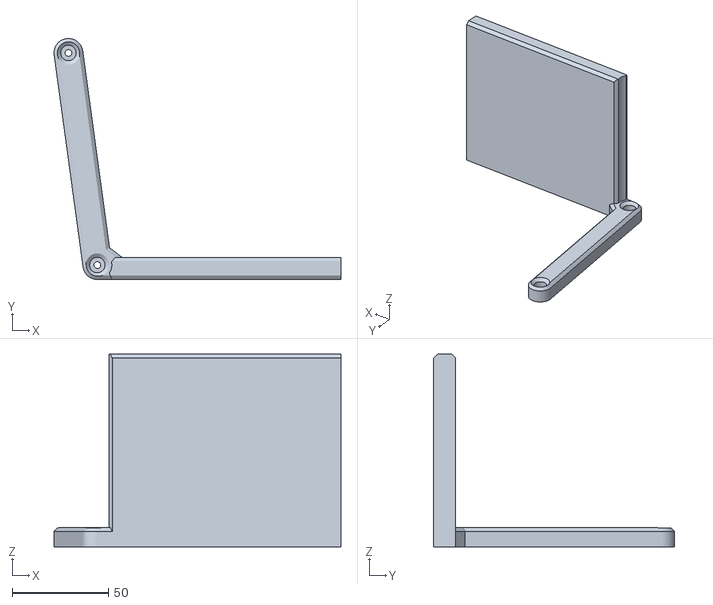
[picture p156: CAD file, 2022-02-13]
QtDash/Hardware/Screen Mounting/Electronics Mount-right.stl
148.9 x 125.1 x 100.0
