whitfijs-jw/Volvo240-DigitalDash/QtDash/Hardware/TachAdapter/Board Revisions/Rev B/tach_adapter_revb_kicad.png

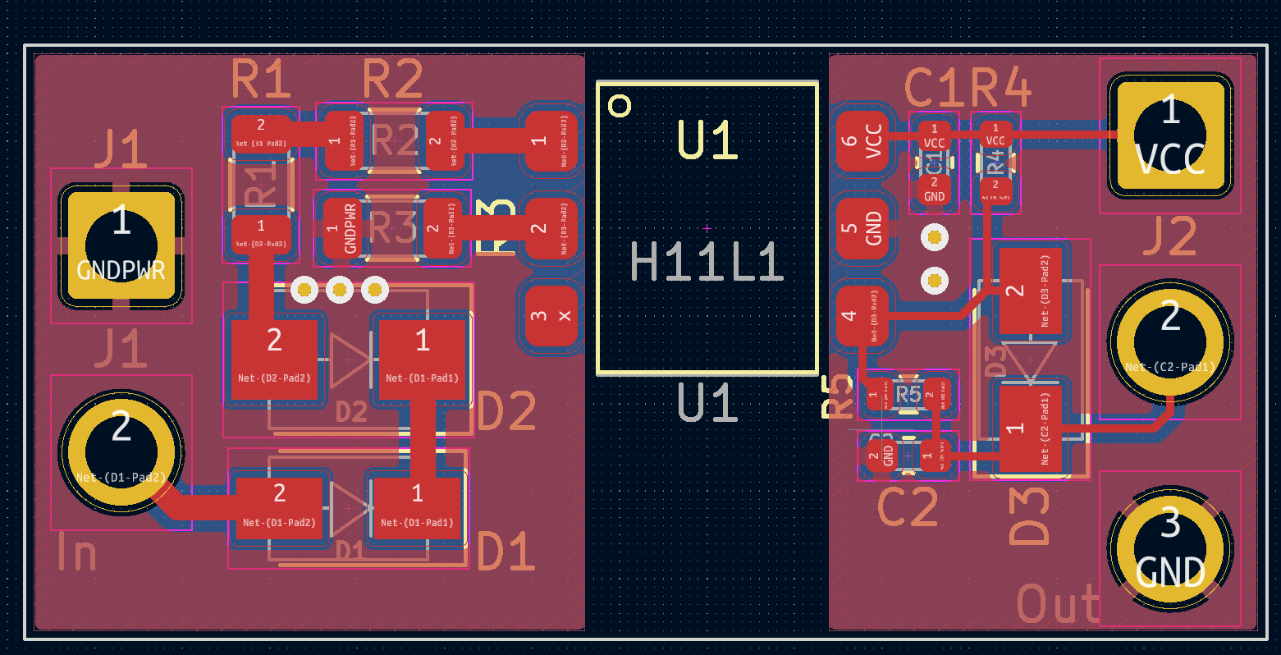
QtDash/Hardware/TachAdapter/Board Revisions/Rev B/tach_adapter_revb_kicad.png
