whitfijs-jw/Volvo240-DigitalDash/QtDash/Hardware/Cold Start Power Supply/Dash Power Supply - Kicad/cold-start-power-supply/schematic/cold-start-power-supply.pdf

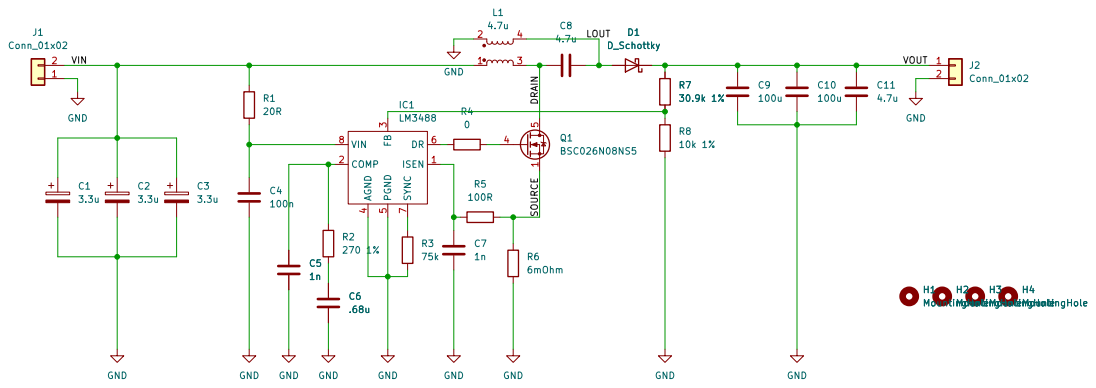
[picture p192: page 1]

File: cold-start-power-supply.kicad_sch Sheet: /
Id: 1/1 Title: Cold Start Power Supply
