whitfijs-jw/Volvo240-DigitalDash/QtDash/Hardware/TouchPanel/touch_panel/Board Revisions/Rev A/touch_panel_schematic_rev_A/touch_panel_rev_A.pdf

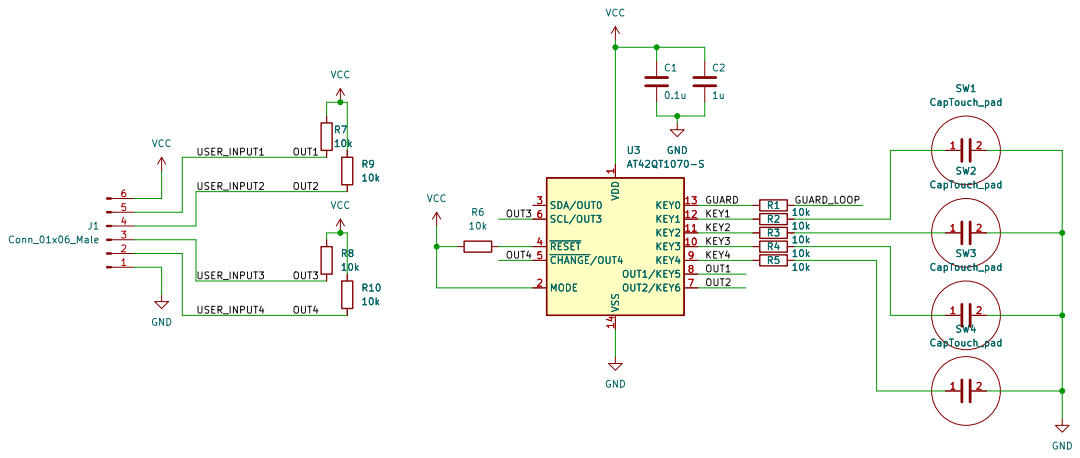
[picture p194: page 1]

1 KEY3 10 KEY2 11 KEY1 12 KEY0 13 VSS 14 MODE 2 SDA/OUT0 3 ~{RESET} 4 ~{CHANGE}/OUT4 5 SCL/OUT3 6 OUT2/KEY6 7 OUT1/KEY5 8 KEY4 9 U3AT42QT1070-S R4 10k R1 10k R7

1 KEY3 10 KEY2 11 KEY1 12 KEY0 13 VSS 14 MODE 2 SDA/OUT0 3 ~{RESET} 4 ~{CHANGE}/OUT4 5 SCL/OUT3 6 OUT2/KEY6 7 OUT1/KEY5 8 KEY4 9 R5 10k R3 10k R1 10k R4 10k R2 10k SW2 CapTouch_pad

File: touch_panel.kicad_sch Sheet: /
Id: 1/1 Title: Volvo 240 Digital Digital Dash Control Panel CapTouch
