whitfijs-jw/Volvo240-DigitalDash/QtDash/Hardware/TachAdapter/Board Revisions/Rev A/tach_adapter.pdf

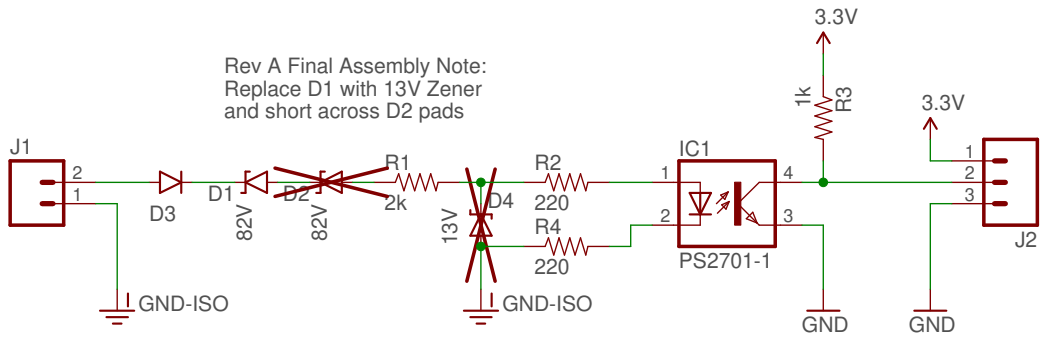
[picture p195: page 1]

Rev A Final Assembly Note: Replace D1 with 13V Zener and short across D2 pads 82V

Document Number: | REV:

Date: 3/24/23 4:56 PM | Sheet: 1/1

3/24/23 4:56 PM f=0.91 /home/whitfijs/git/Volvo240-DigitalDash/QtDash/Hardware/TachAdapter/Board Revisions/Rev A/tach_adapter.sch (Sheet: 1/1)
