whitfijs-jw/Volvo240-DigitalDash/QtDash/Hardware/DashHat/Board Revisions/Rev A/dash-hat.pdf

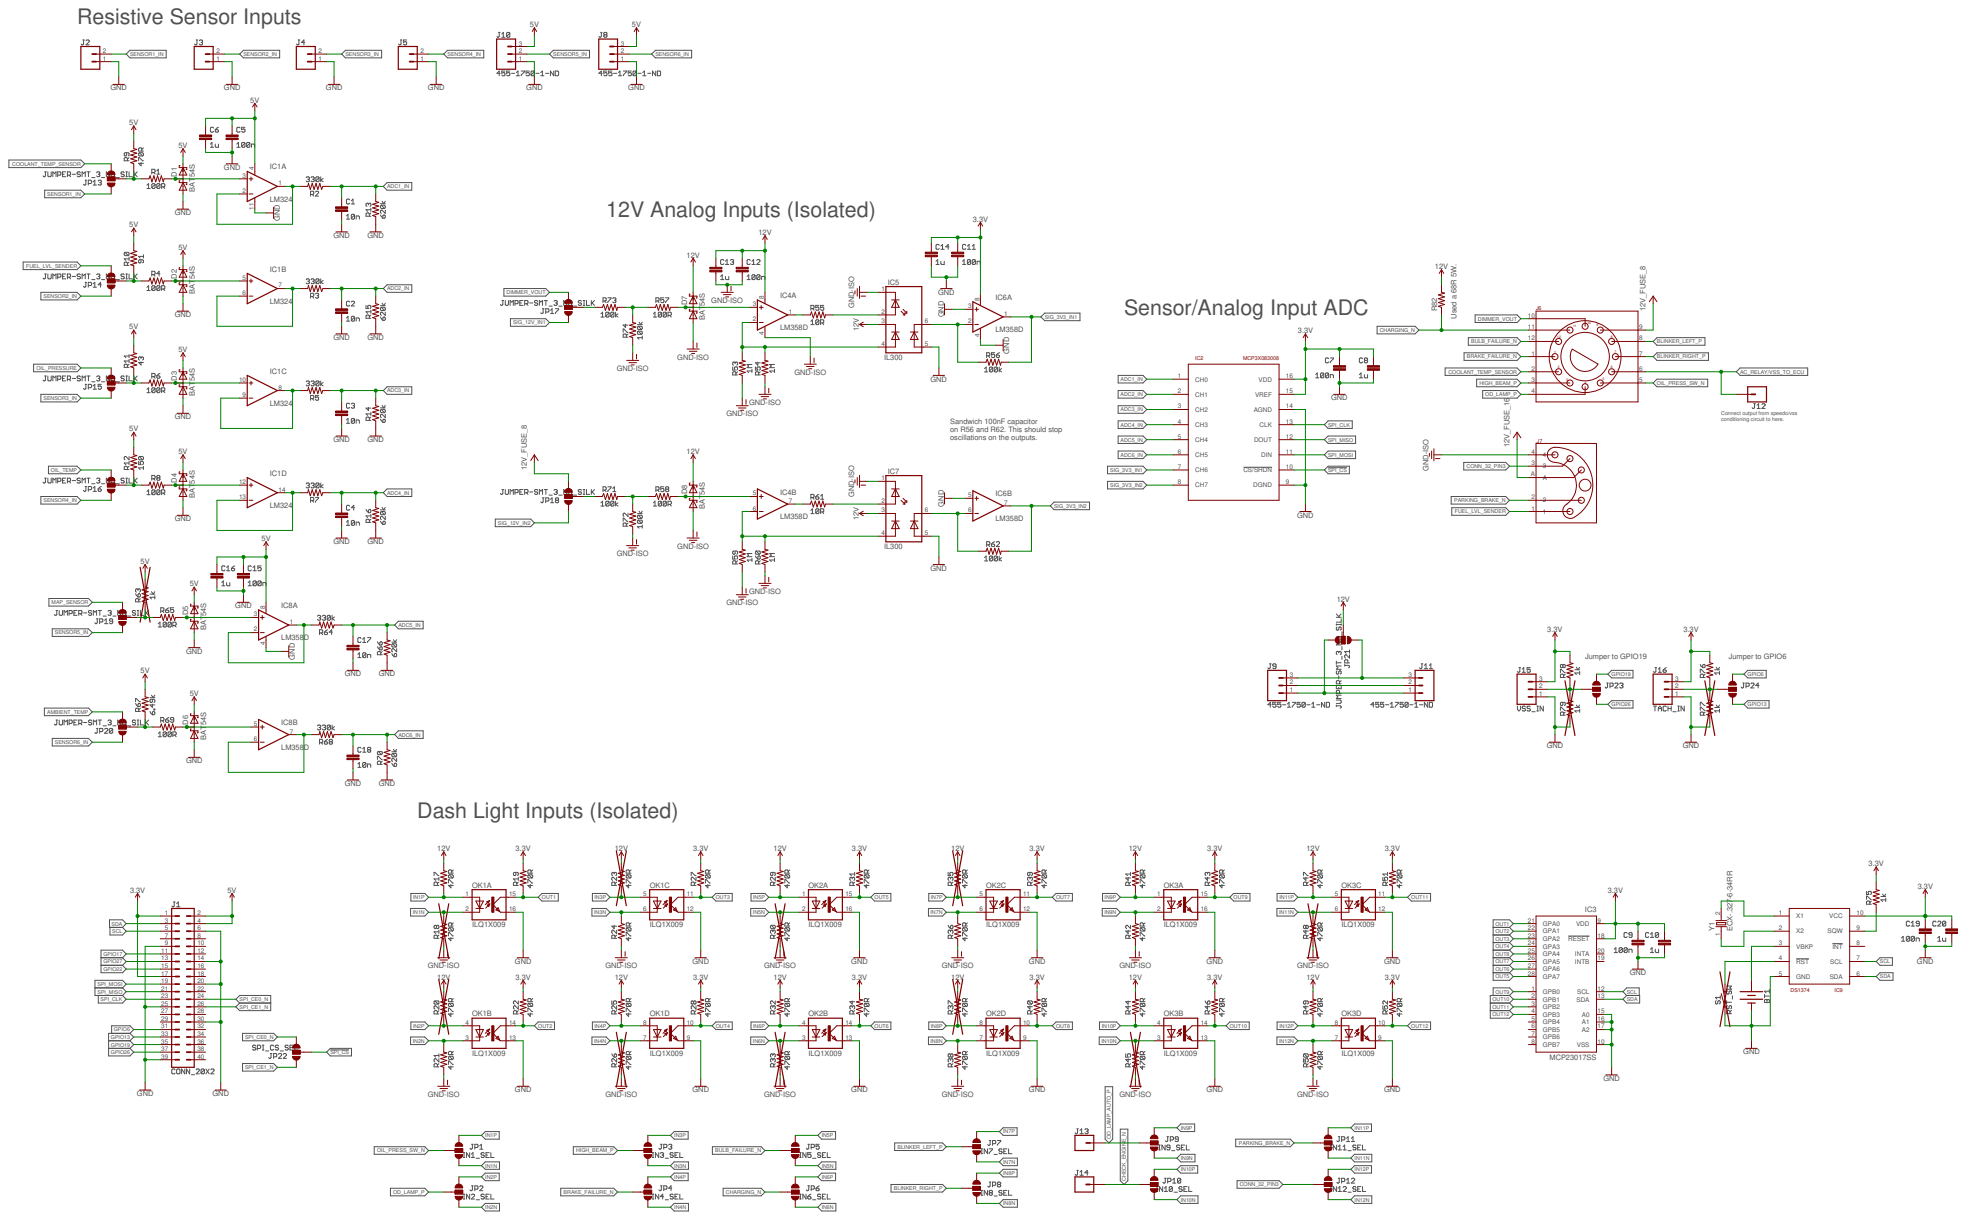
[picture p196: page 1]

GND-ISO

Sensor/Analog Input ADC

Connect output from speedo/vss

conditioning circuit to here. Sandwich 100nF capacitor on R56 and R62. This should stop
oscillations on the outputs.

GND
Dash Light Inputs (Isolated)
