whitfijs-jw/Volvo240-DigitalDash/QtDash/Hardware/Simulation/inputs_sim.asc

C1: cap; 10n
C2: cap; 100n
D1: schottky; BAT54
D2: schottky; BAT54
R1: res; 640k
R2: res; 330k
R3: res; 1k
R4: res; 6k
R5: res; 100
R6: res; 10Meg
R7: res; 470
R8: res; 470
R9: res; 0
R10: res; 470
R11: res; 470
R12: res; 0
R13: res; 270
R14: res; 100k
R15: res; 100k
R16: res; 100k
R17: res; 20k
S1: sw; MYSW
S2: sw; MYSW
U1: opamp
U2: 4N25
U3: 4N25
U4: IL300
U5: UniversalOpamp
U6: UniversalOpamp
V1: voltage; 5; AC 1
V2: voltage; PULSE(0 12 0 100u 100u 2 4)
V3: voltage; 3.3
V4: voltage; 12
V5: voltage; SINE(2.5420 1.7437 1)
V6: voltage; SINE(12 6 1)
Named nets: 0, Signal, 3.3V, 12V, signal, VBAT
;.ac dec 1024 1u 500
.lib opamp.sub
.tran 5
;.step param R 190 6k 100
;op 5
.model MYSW SW(Ron=0.5 Roff=1Meg Vt=.5 Vh=-.4)
