whitfijs-jw/Volvo240-DigitalDash/QtDash/Hardware/Simulation/coil_sim.asc

A1: schmtbuf
C1: cap; .25µ
C2: cap; 10p
C3: cap; 10p
D1: diode; RR1VWM4S
D2: zener; BZX84C13VL
D3: zener; BZX84C13VL
D4: diode; 1N4148
D6: diode
L1: ind2; 1m
L2: ind2; 1; Rser=0
R1: res; 100
R2: res; 0.5
R3: res; 220
R4: res; 220
R5: res; 1k
R6: res; 220
R7: res; 800
S1: sw; MYSW
U1: PC817A
V1: voltage; PULSE(0 5 0 10n 10n 12m 20m)
V2: voltage; 12
V3: voltage; 3.3
Named nets: 0, CoilN
.model MYSW SW(Ron = 1m Roff = 10Meg Vt = 1.5)
K1 L1 L2 1
.tran 250m
