whitfijs-jw/Volvo240-DigitalDash/QtDash/Hardware/Simulation/power_failover.asc

C1: cap; 100n
C2: cap; 10µ
R1: res; 100k
R2: res; 21.5k
R3: res; 140
R4: res; 140
R5: res; 5
U1: LTC4415
V1: voltage; PULSE(5 0 1 10m 5 1 0)
V2: voltage; 5
Named nets: 0
.tran 0 10 1n
