whitfijs-jw/Volvo240-DigitalDash/QtDash/VolvoDigitalDashModels/app/inc/ll/vss_input.h

#ifndef VSS_INPUT_H
#define VSS_INPUT_H

#include <config.h>
#include <string>
#include <iostream>
#include <fstream>
#include <cstdio>
#include <cstring>
#include <filesystem>
#include <map>
#include <cmath>
#include <sensor_utils.h>
#include <pulse_counter.h>

/**
 * @brief Class to transform pulse spacing information from
 * VSS (vehicle speed sensor) sensor
 */
class VssInput : public PulseCounter {
public:

    /**
     * @brief VssInput constructor
     * @param config: VSS sensor configuration
     * @param path: path to vss_counter kernel module output
     */
    VssInput(const SensorConfig::VssInputConfig& config,
             const std::string& path = DEFAULT_VSS_PULSE_PATH) :
        PulseCounter(path), mConfig(config) {
        if (mConfig.pulsePerUnitDistance <= 0 && mConfig.tireDiameter > 0) {
            // we need to calculate from tire diameter
            qreal circumference = SensorUtils::toMiles(mConfig.tireDiameter, mConfig.tireDiameterUnits) * M_PI;

            mConfig.pulsePerUnitDistance = std::ceil(1 / circumference * mConfig.pulsePerRot);
            mConfig.distanceUnits = Units::DistanceUnits::MILE;
        }

        // adjust min pulse spacing
        qDebug() << "VSS Max Frequency" << mConfig.maxSpeed / 3600.0 * mConfig.pulsePerUnitDistance;
        setMaxFrequency(mConfig.maxSpeed / 3600.0 * mConfig.pulsePerUnitDistance);
    }

    /**
     * @brief Get speed in mph
     * @return speed in mph
     */
    qreal getMph() const {
        qreal pulsesPerSecond = getFrequency();
        return pulsesPerSecond * (1.0 / mConfig.pulsePerUnitDistance) * 3600.0;
    }

    /**
     * @brief Get speed in kph
     * @return speed in kph
     */
    qreal getKph() const {
        qreal mph = getMph();
        return SensorUtils::toMeters(mph, Units::DistanceUnits::MILE) / 1000.0;
    }


private:
    static constexpr char DEFAULT_VSS_PULSE_PATH[] = "/sys/class/volvo_dash/vss_counter/"; //!< default pulse counter location
    SensorConfig::VssInputConfig mConfig; //!< VSS configuration
};

#endif // VSS_INPUT_H
